Nguyen-code/TVCRocket/Software/Reference/aeroForcesCalc1.jpg

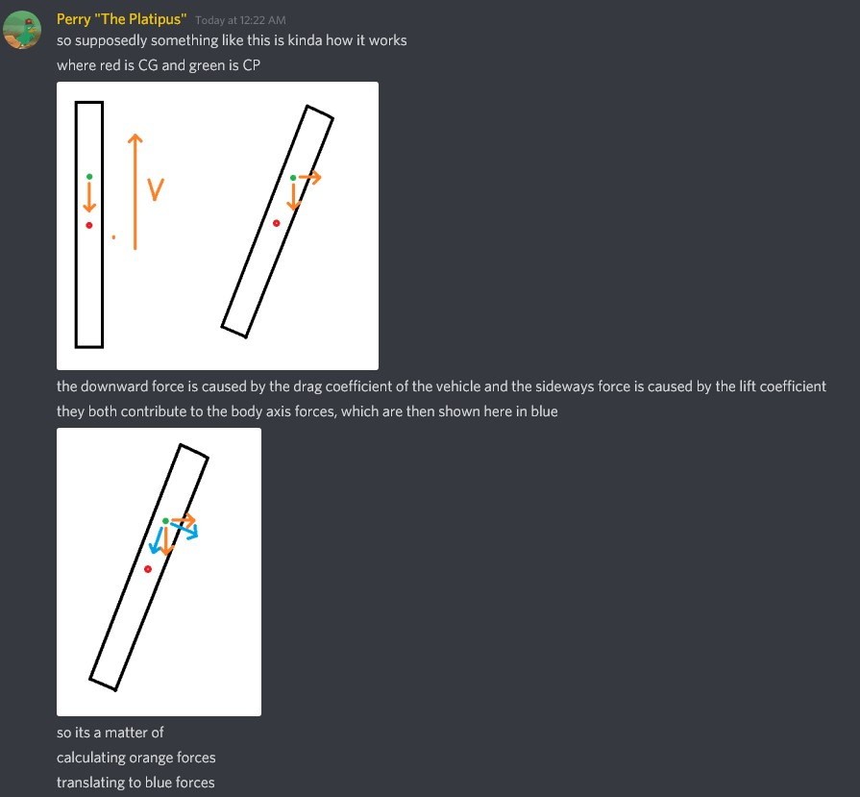
Software/Reference/aeroForcesCalc1.jpg
