Nguyen-code/TVCRocket/Software/Reference/aeroForcesCalc2.jpg

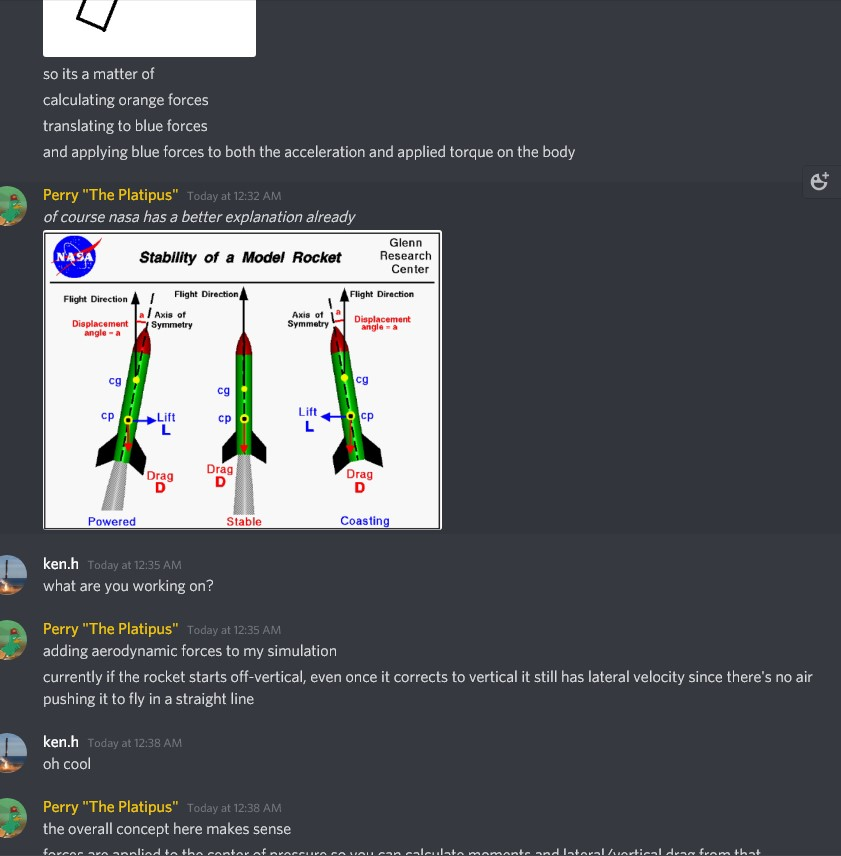
Software/Reference/aeroForcesCalc2.jpg
