Nguyen-code/TVCRocket/Software/Reference/aeroForcesCalc3.jpg

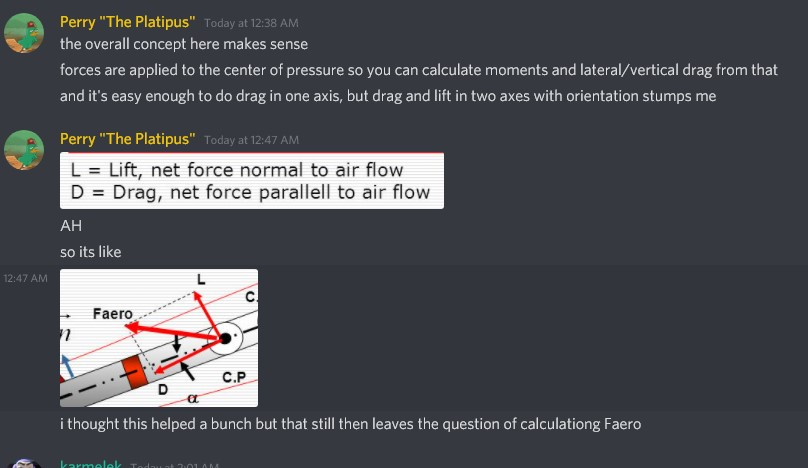
Software/Reference/aeroForcesCalc3.jpg
