Nguyen-code/TVCRocket/Software/Reference/axesCheck.jpg

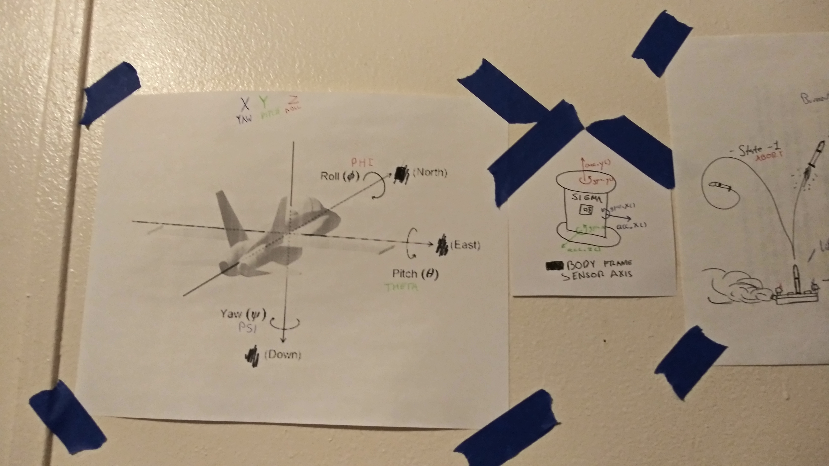
Software/Reference/axesCheck.jpg
