Nguyen-code/TVCRocket/Software/Reference/BEST PROPER USB DIAGRAM.jpg

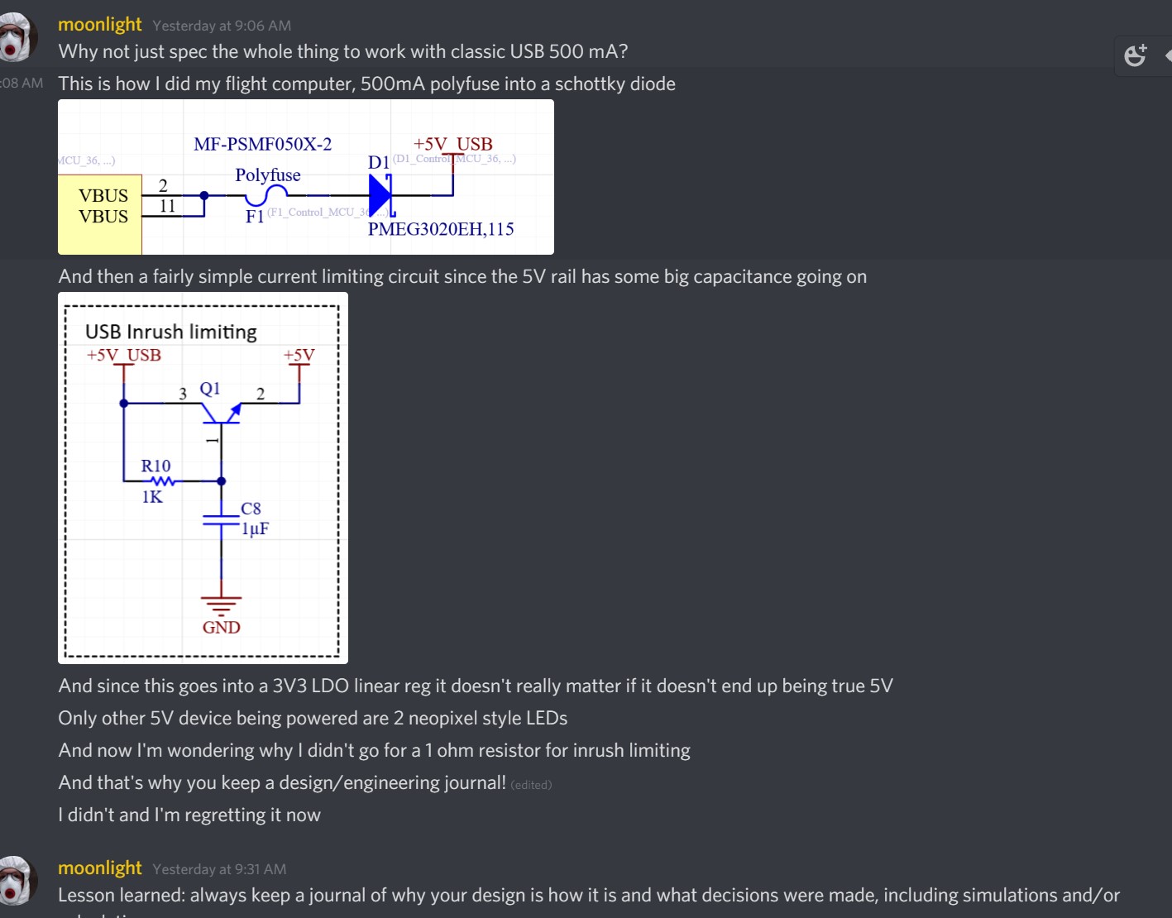
Software/Reference/BEST PROPER USB DIAGRAM.jpg
