Nguyen-code/TVCRocket/Software/Reference/bitfields.jpg

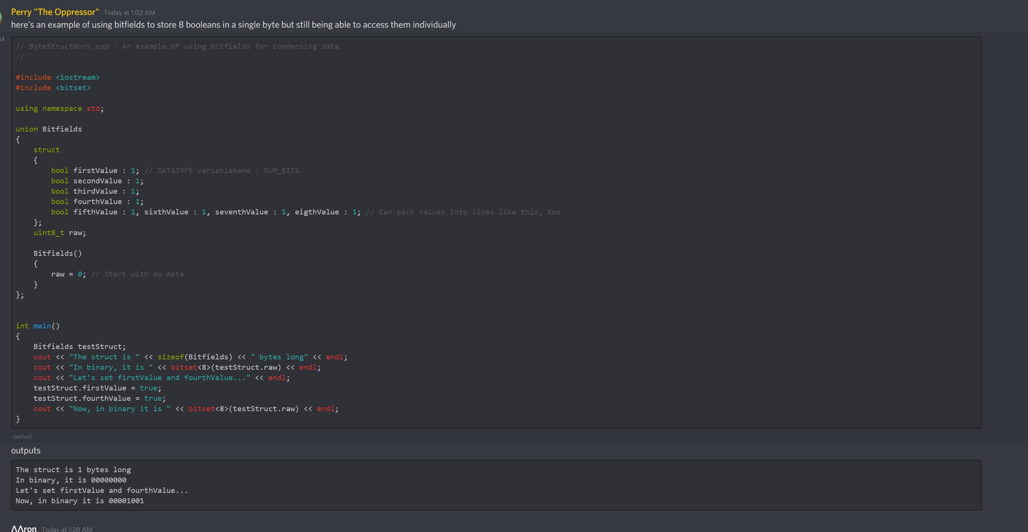
Software/Reference/bitfields.jpg
