Nguyen-code/TVCRocket/Software/Reference/dma spi.jpg

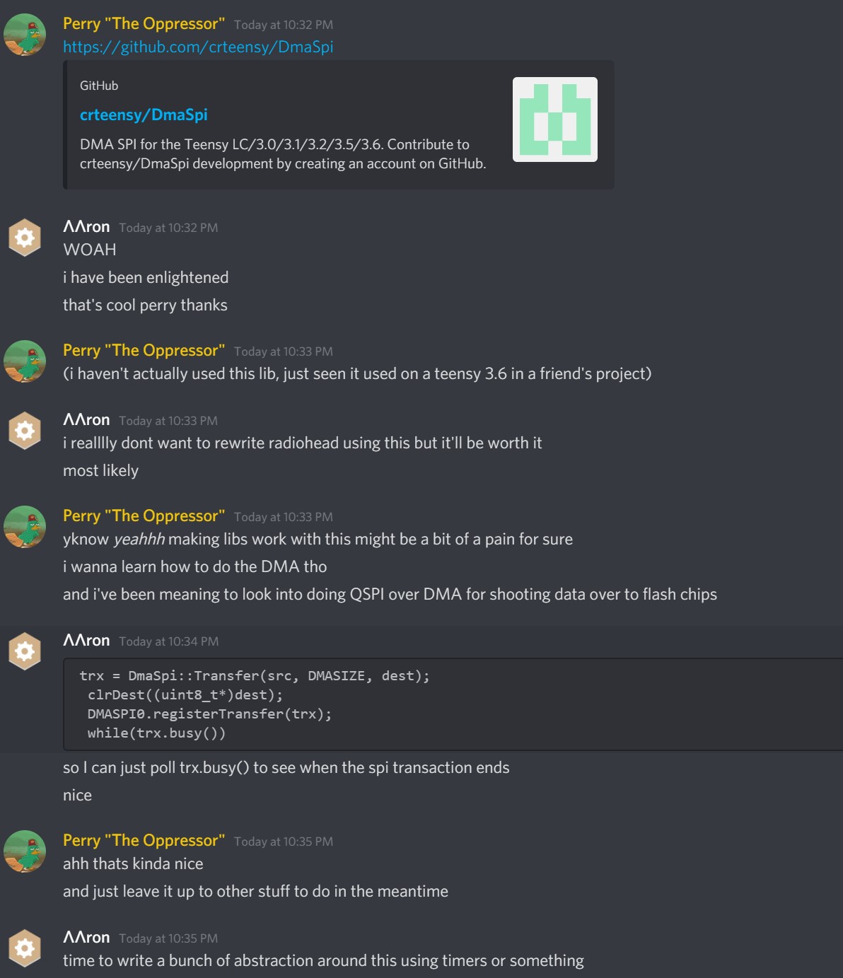
Software/Reference/dma spi.jpg
