Nguyen-code/TVCRocket/Software/Reference/drag and tvc.jpg

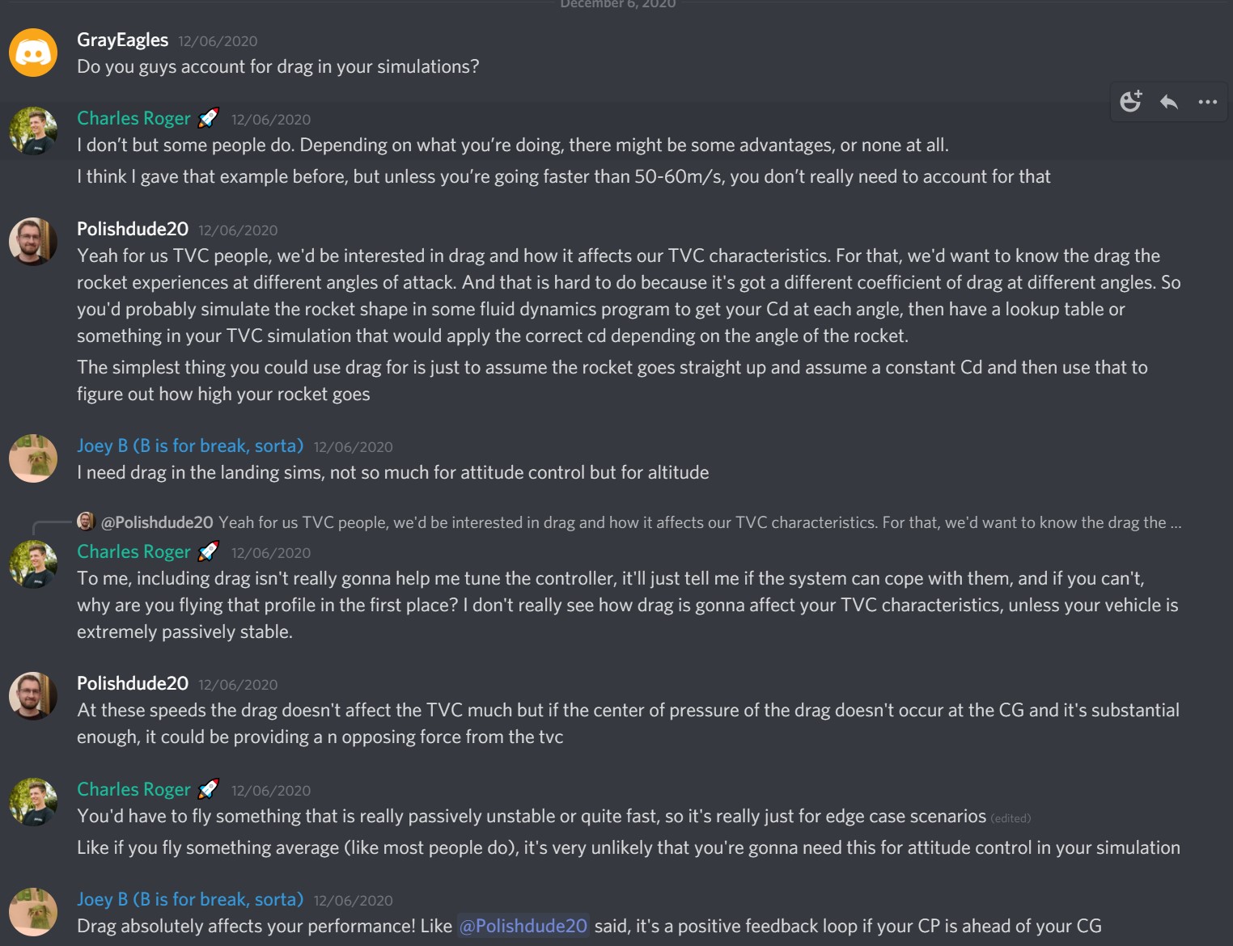
Software/Reference/drag and tvc.jpg
