Nguyen-code/TVCRocket/Software/Reference/ground software idea.jpg

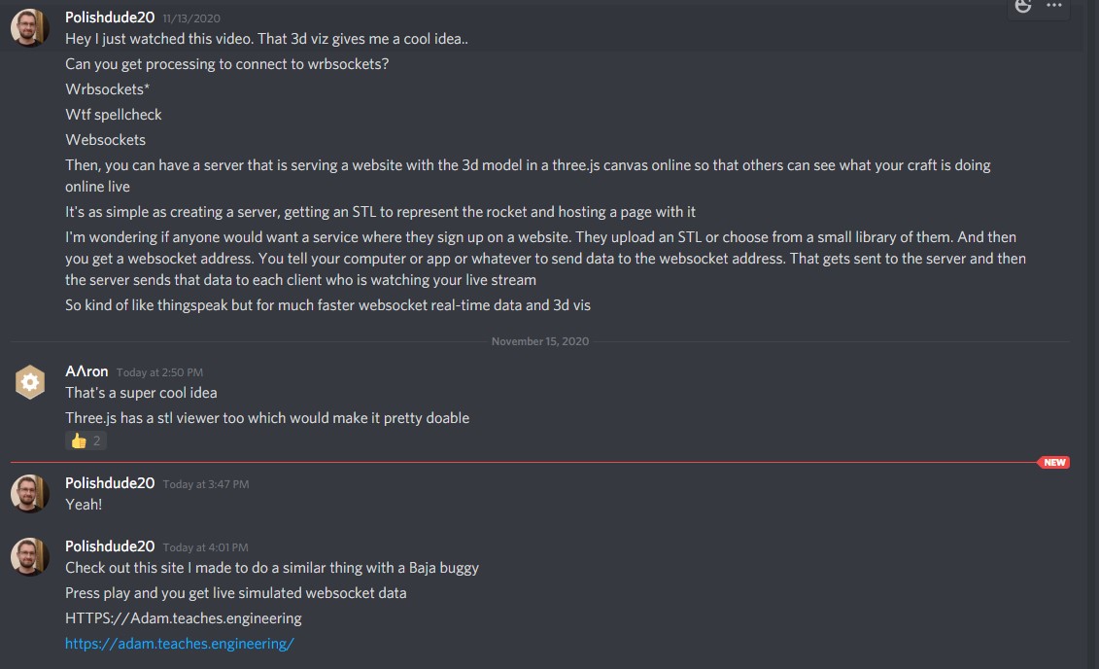
Software/Reference/ground software idea.jpg
