Nguyen-code/TVCRocket/Software/Reference/Holddown_base_v1.png

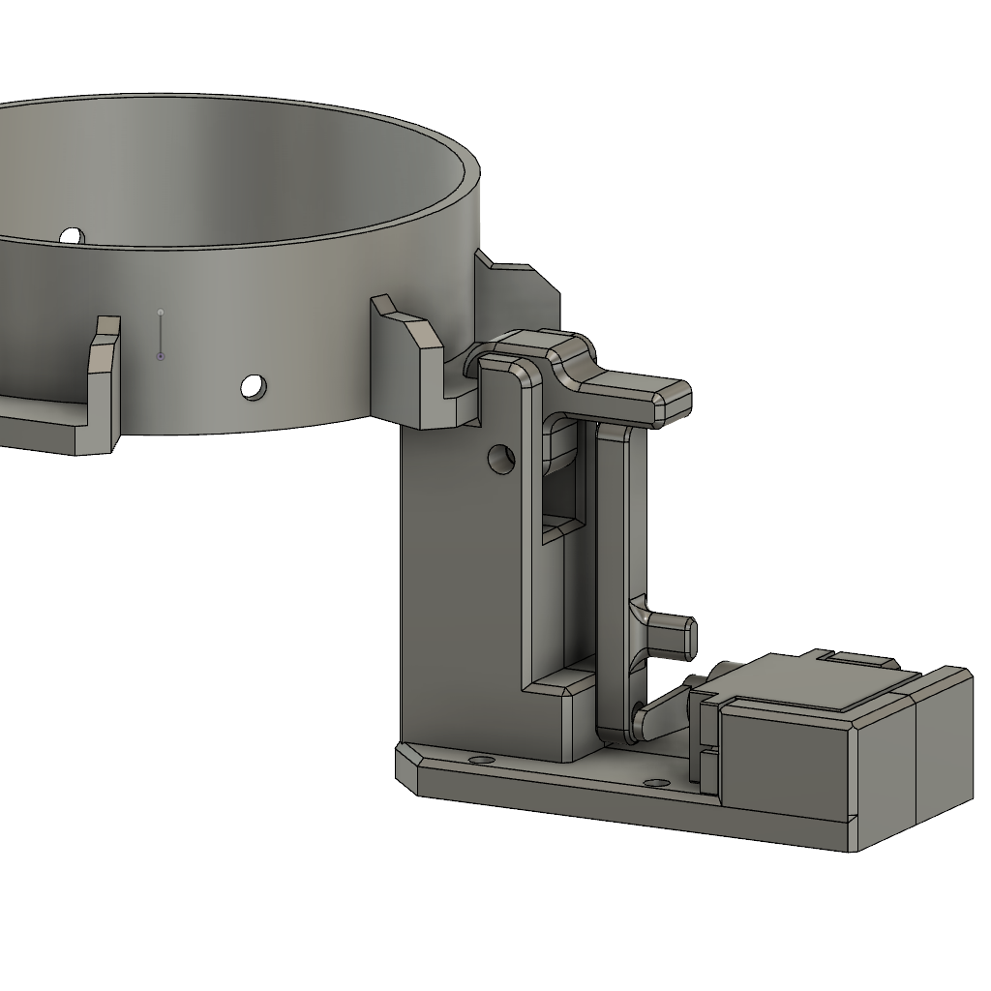
Software/Reference/Holddown_base_v1.png
