Nguyen-code/TVCRocket/Software/Reference/liftoff ori.jpg

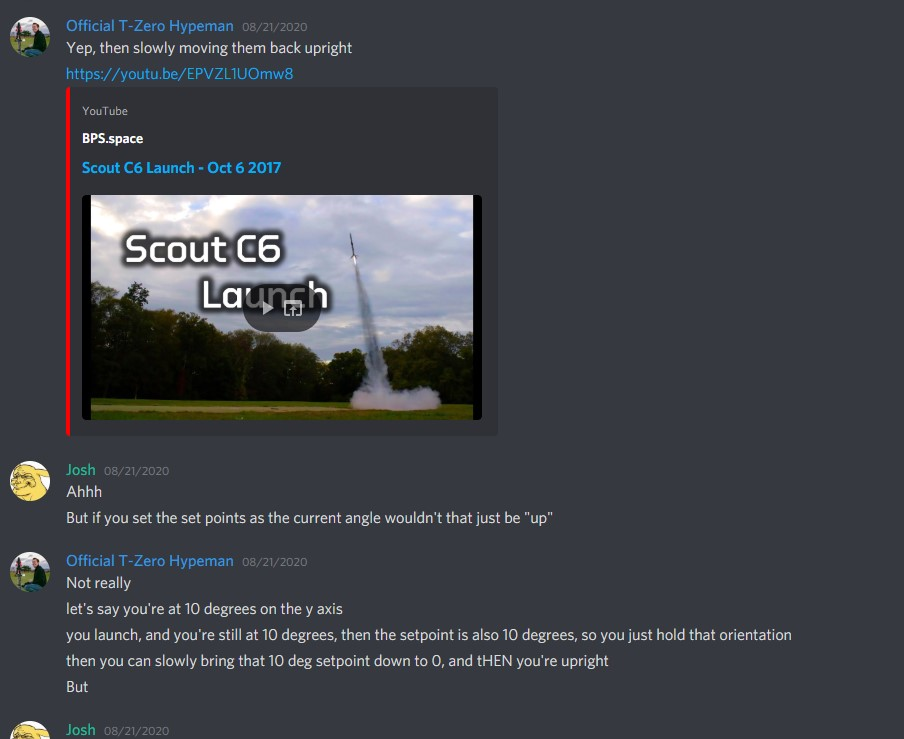
Software/Reference/liftoff ori.jpg
