Nguyen-code/TVCRocket/Software/Reference/local-global quat.jpg

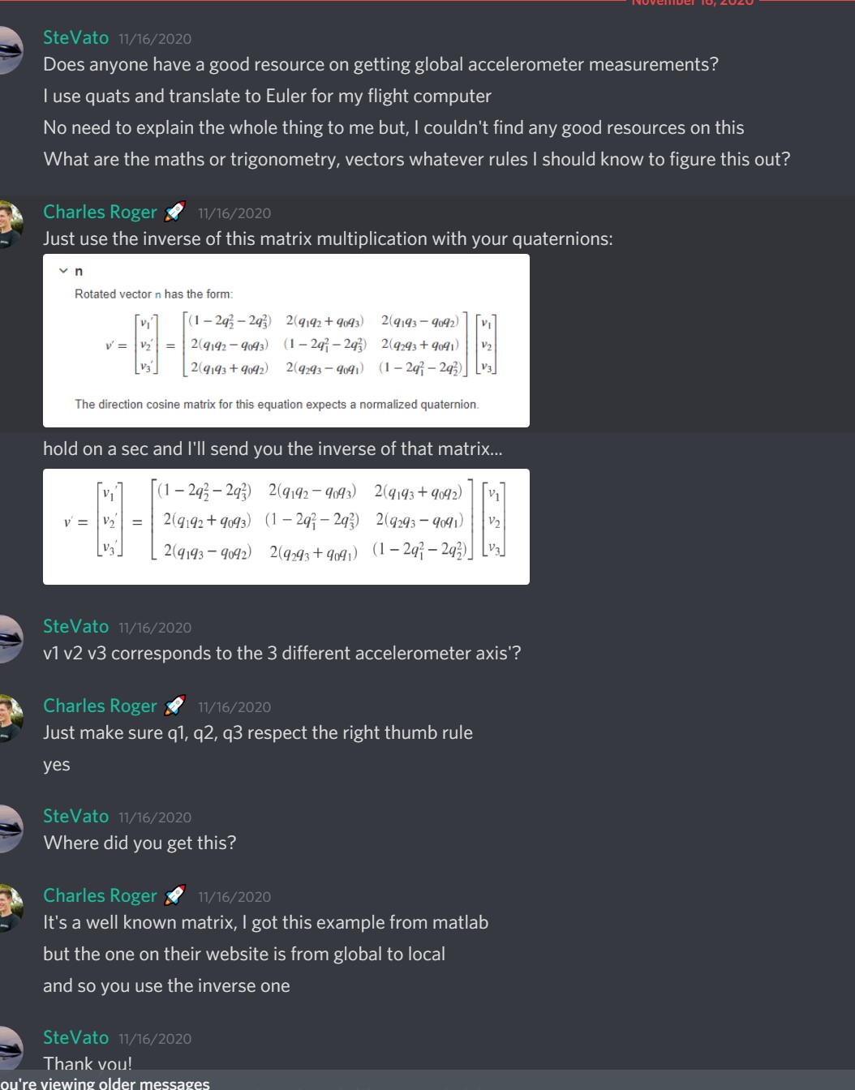
Software/Reference/local-global quat.jpg
