Nguyen-code/TVCRocket/Software/Reference/mag complementary filter.jpg

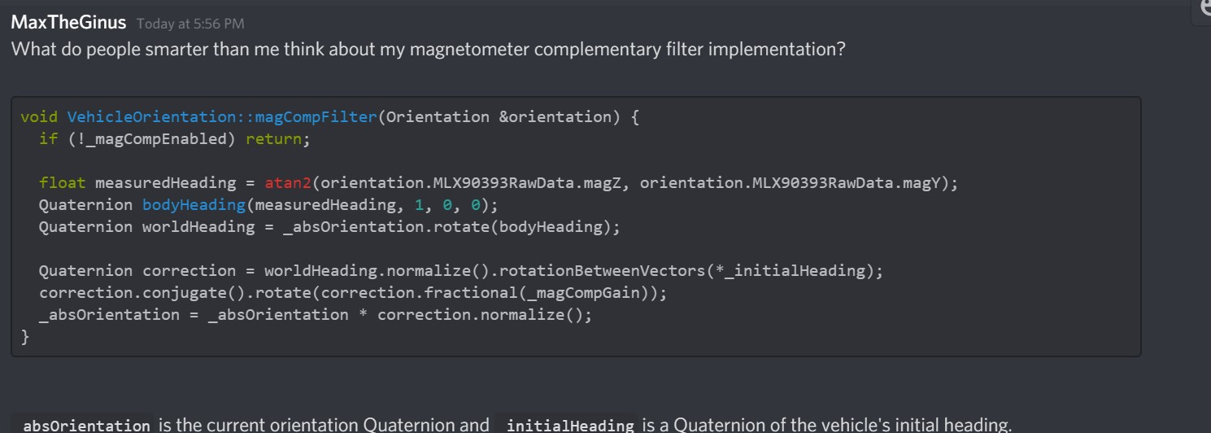
Software/Reference/mag complementary filter.jpg
