Nguyen-code/TVCRocket/Software/Reference/memz.png

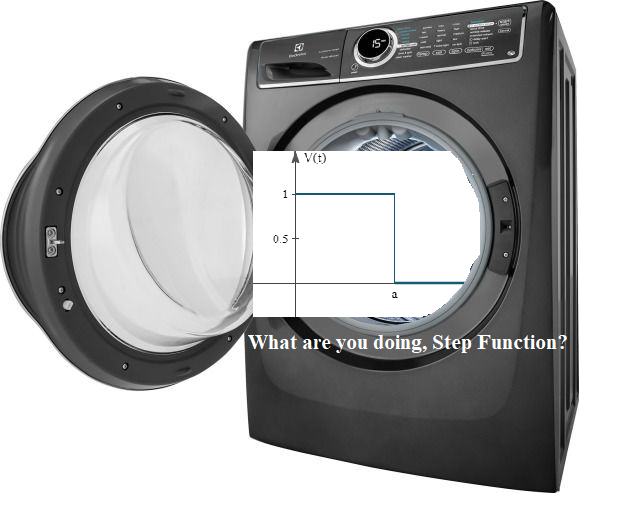
Software/Reference/memz.png
