Nguyen-code/TVCRocket/Software/Reference/mmoi eqn.jpg

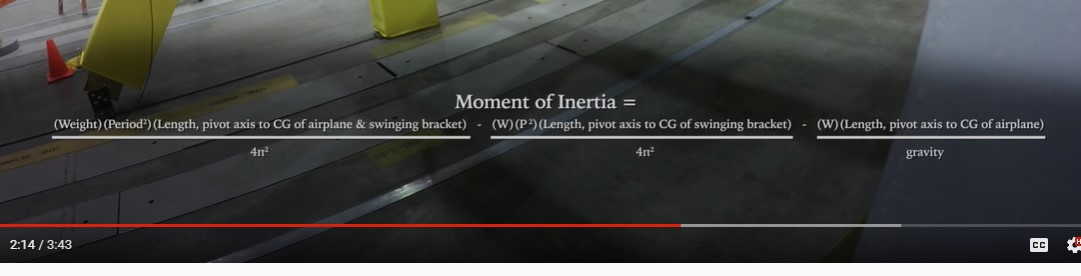
Software/Reference/mmoi eqn.jpg
