Nguyen-code/TVCRocket/Software/Reference/more tvc diode usb stuff.jpg

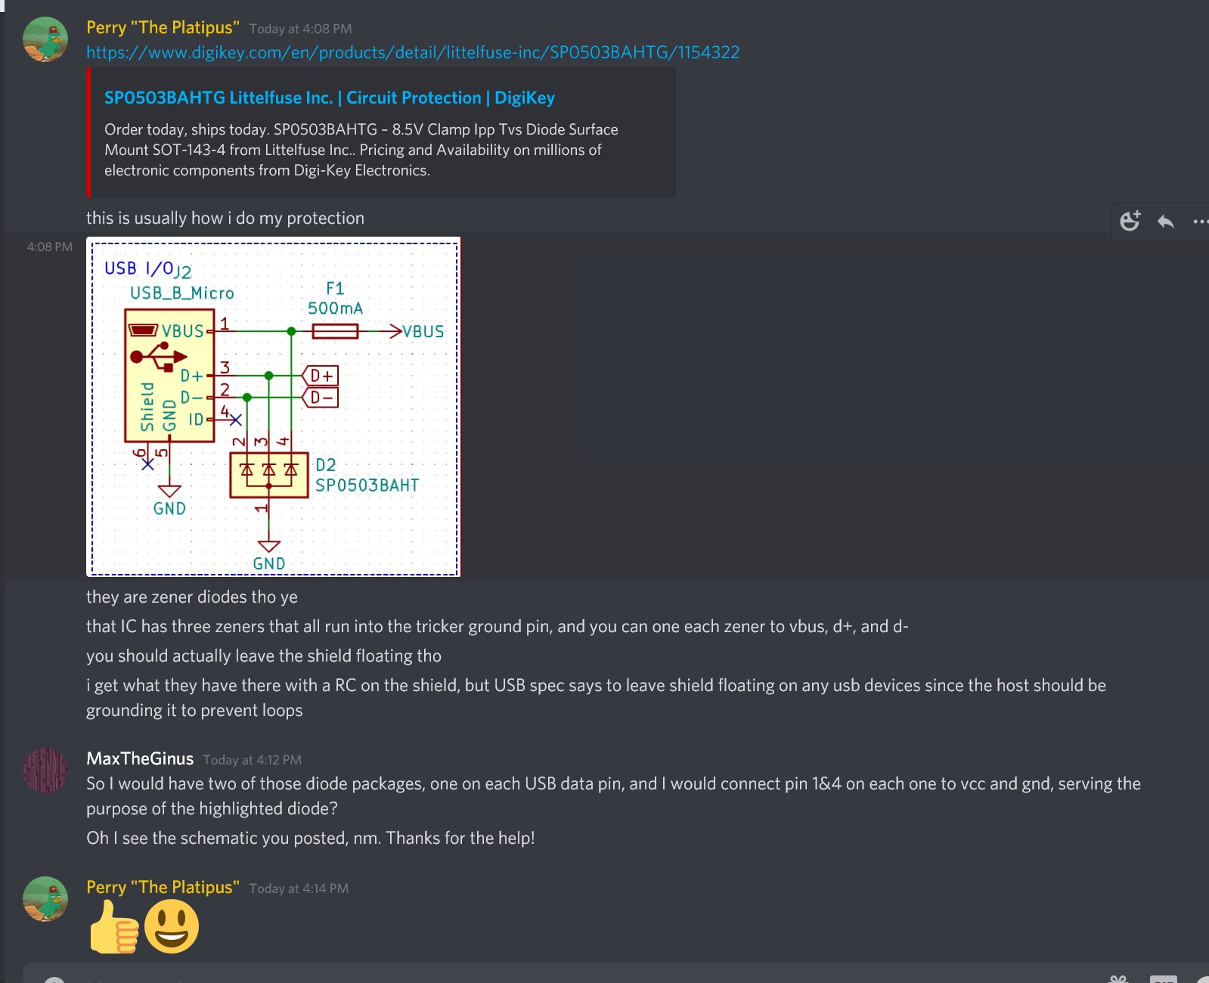
Software/Reference/more tvc diode usb stuff.jpg
