Nguyen-code/TVCRocket/Software/Reference/moreRollWheelControl.jpg

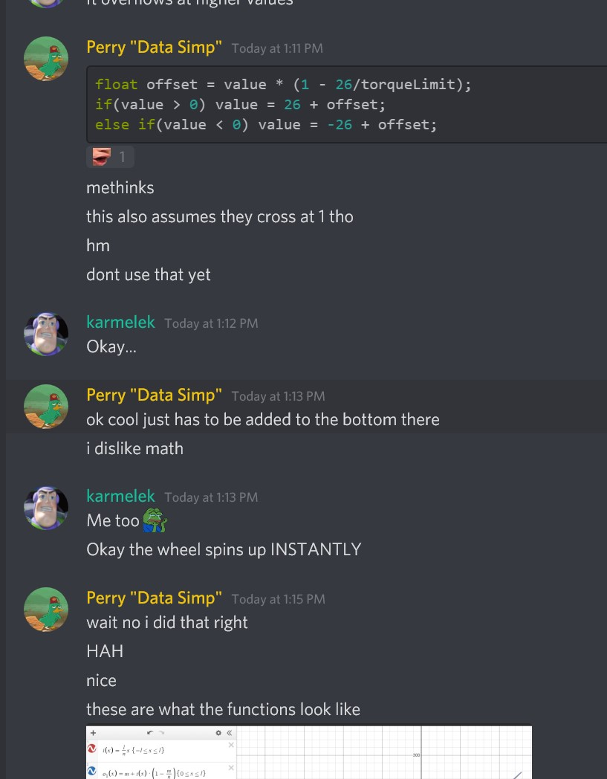
Software/Reference/moreRollWheelControl.jpg
