Nguyen-code/TVCRocket/Software/Reference/morezeroorderhold.png

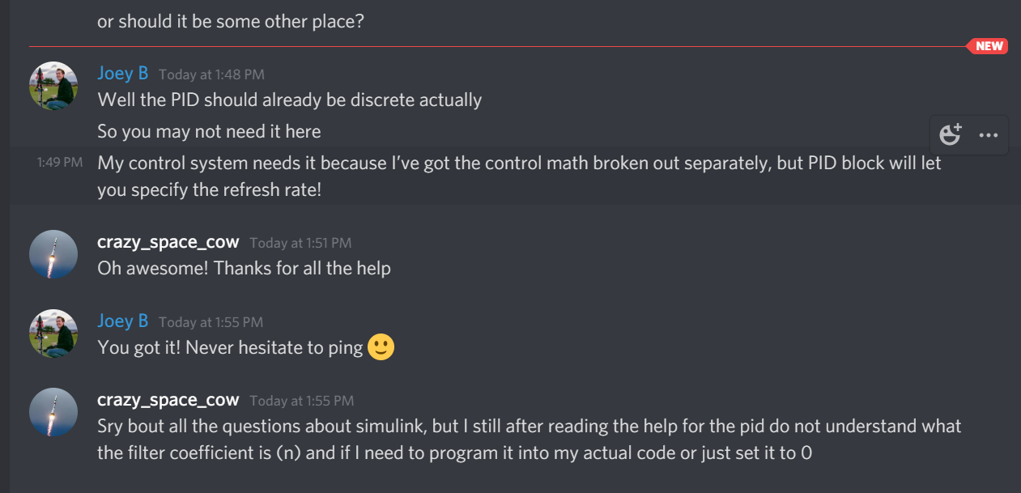
Software/Reference/morezeroorderhold.png
