Nguyen-code/TVCRocket/Software/Reference/nonblocking - use return type of a nonblocking float w status boolean and data.jpg

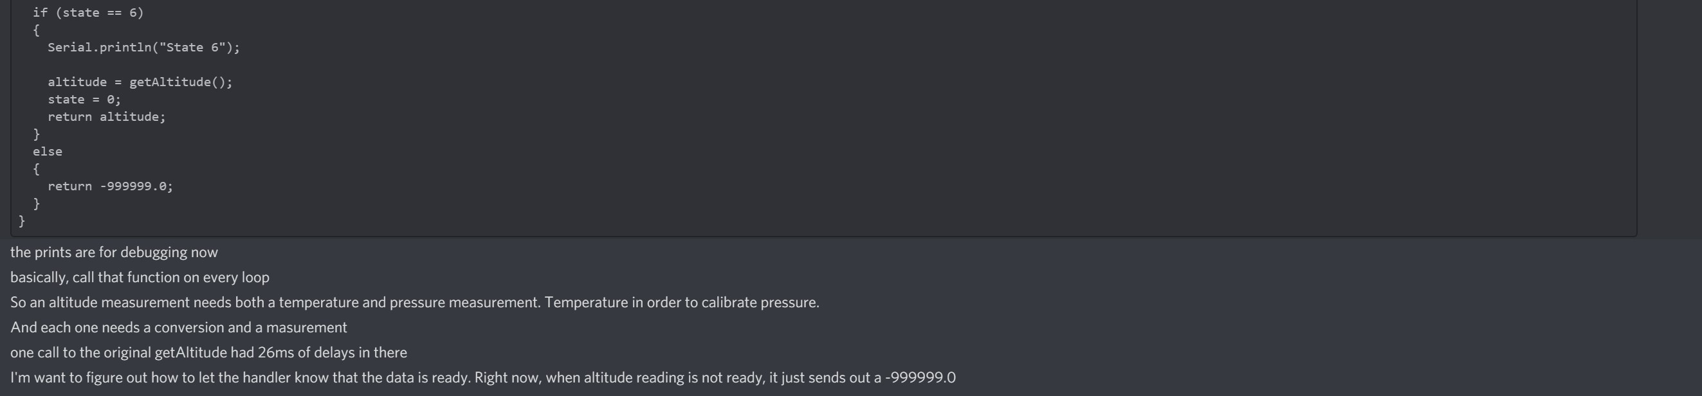
Software/Reference/nonblocking - use return type of a nonblocking float w status boolean and data.jpg
