Nguyen-code/TVCRocket/Software/Reference/pitchManuever.PNG

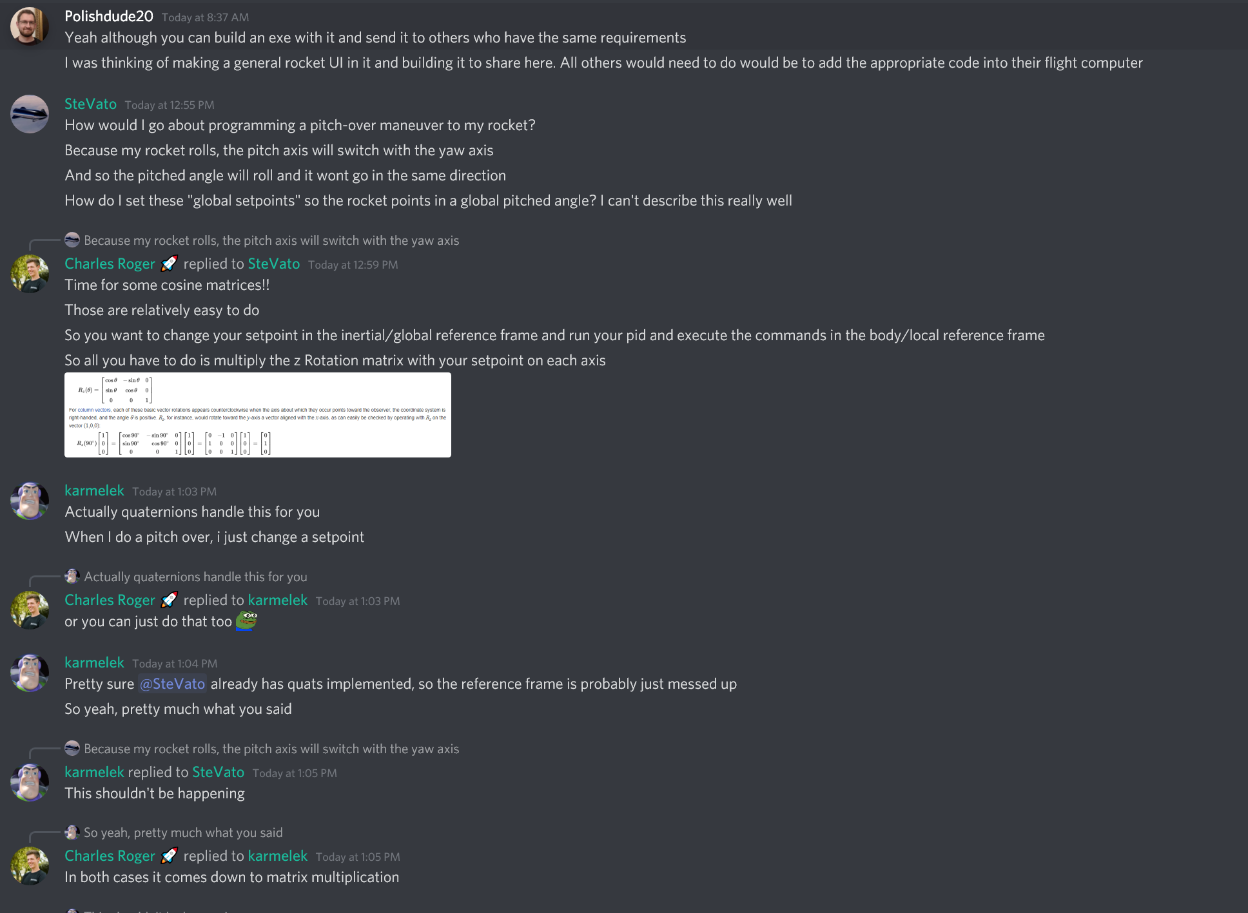
Software/Reference/pitchManuever.PNG
