Nguyen-code/TVCRocket/Software/Reference/quat to ang.jpg

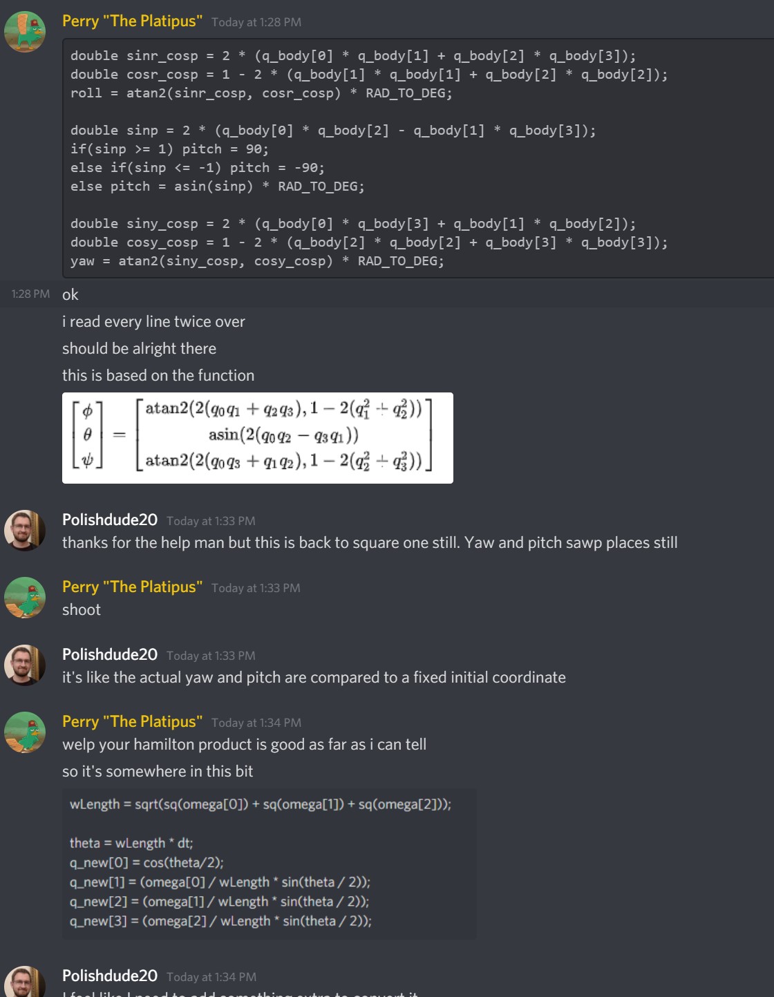
Software/Reference/quat to ang.jpg
