Nguyen-code/TVCRocket/Software/Reference/ref quat ori.png

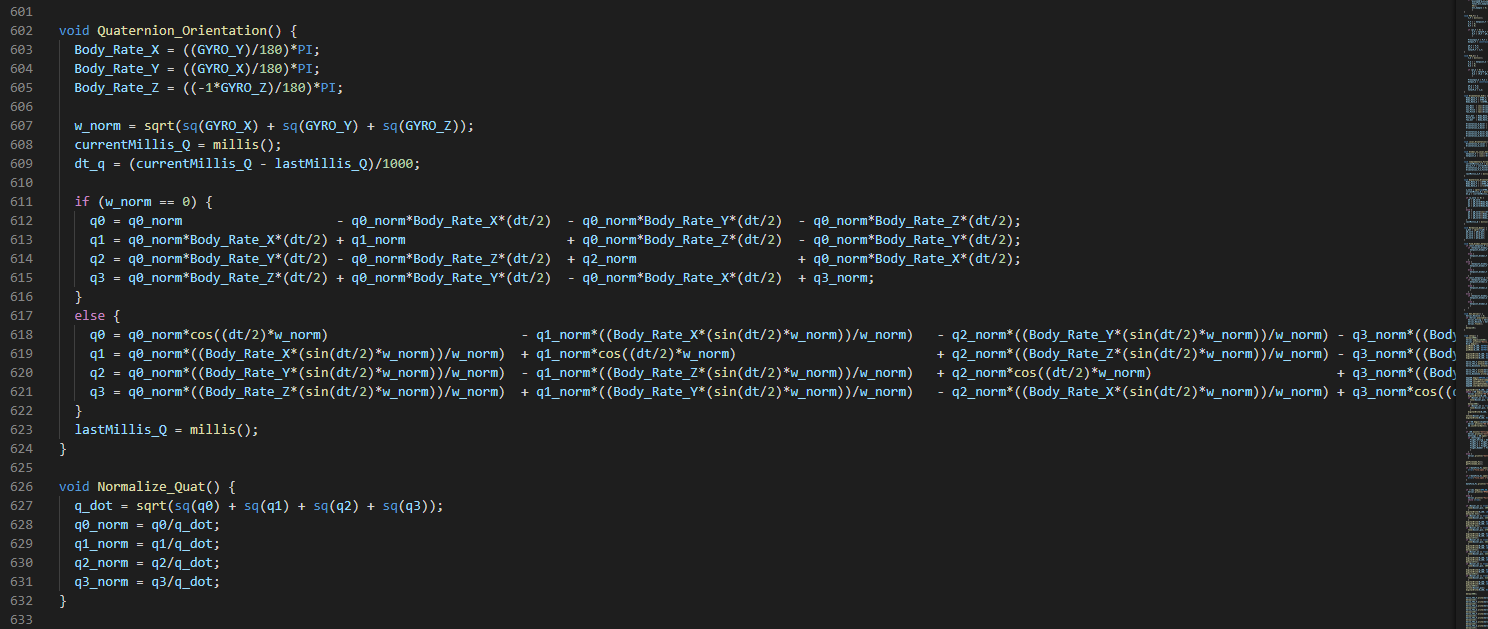
Software/Reference/ref quat ori.png
