Nguyen-code/TVCRocket/Software/Reference/rh v lh coordinate inertial to body.PNG

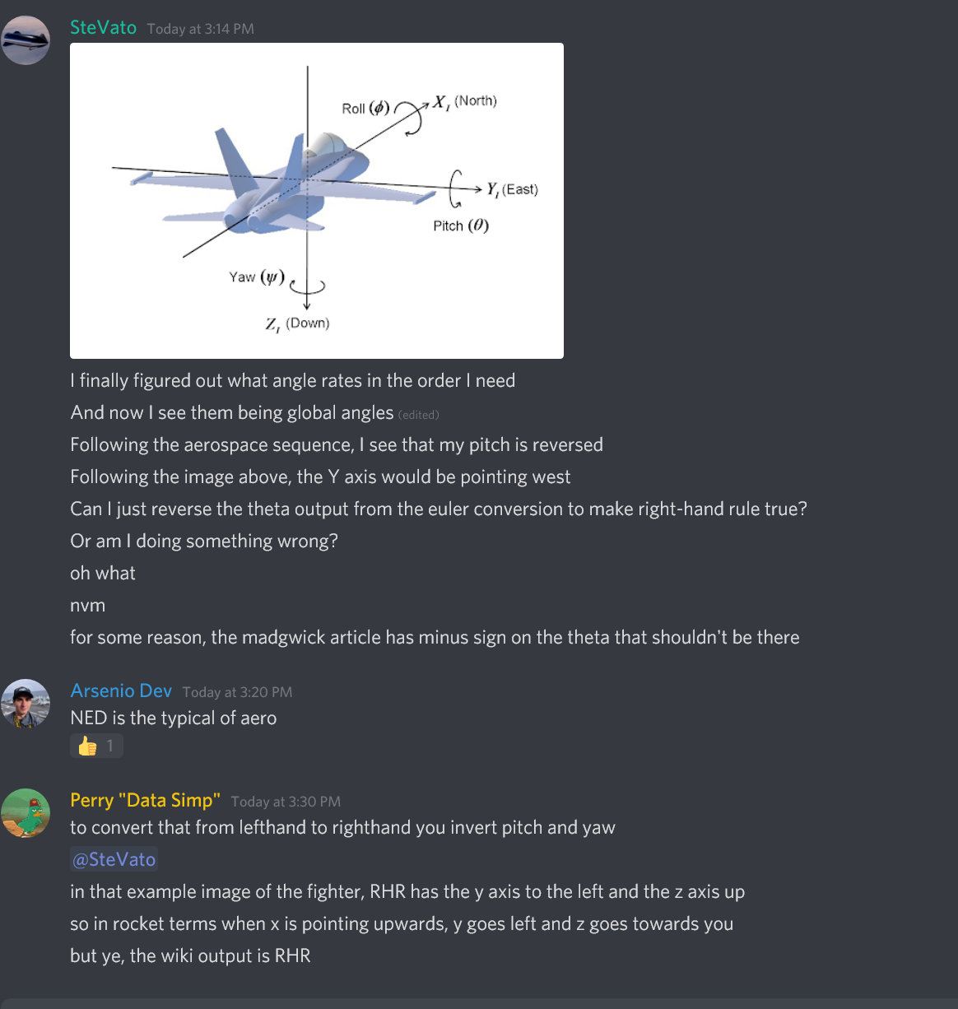
Software/Reference/rh v lh coordinate inertial to body.PNG
