Nguyen-code/TVCRocket/Software/Reference/rollControlcodes.jpg

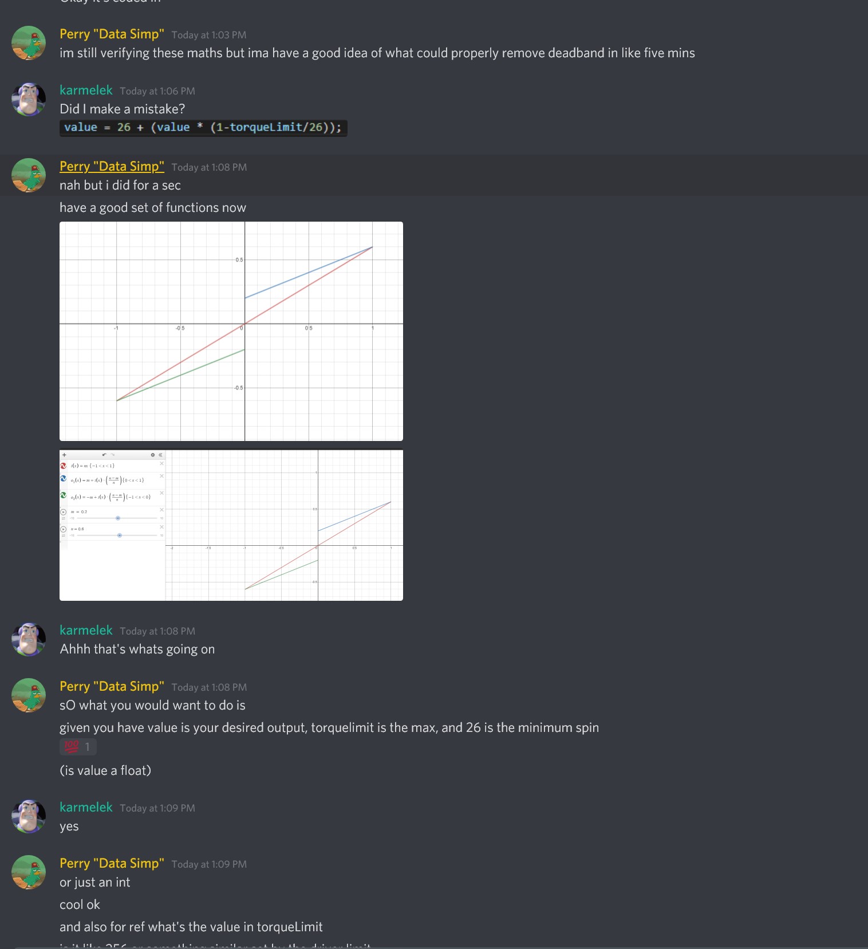
Software/Reference/rollControlcodes.jpg
