Nguyen-code/TVCRocket/Software/Reference/Screenshot 2020-10-27 151349.png

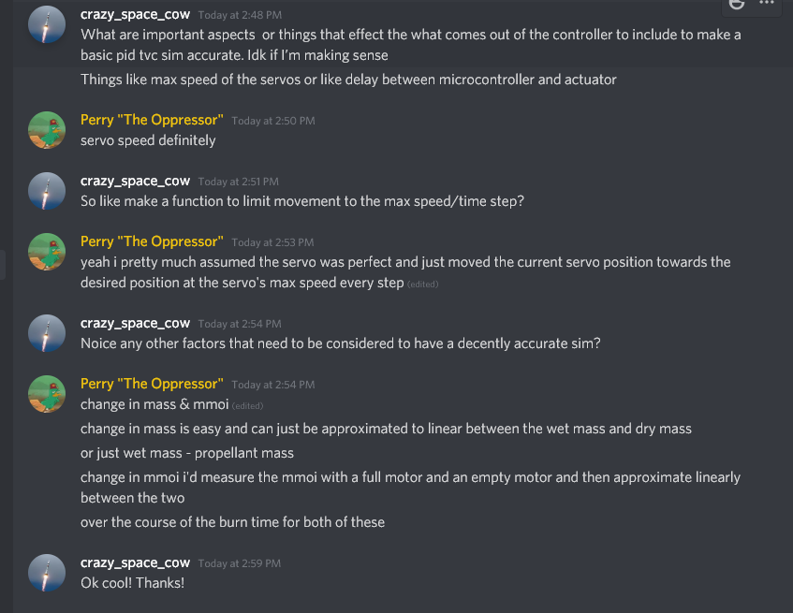
Software/Reference/Screenshot 2020-10-27 151349.png
