Nguyen-code/TVCRocket/Software/Reference/simulink2.png

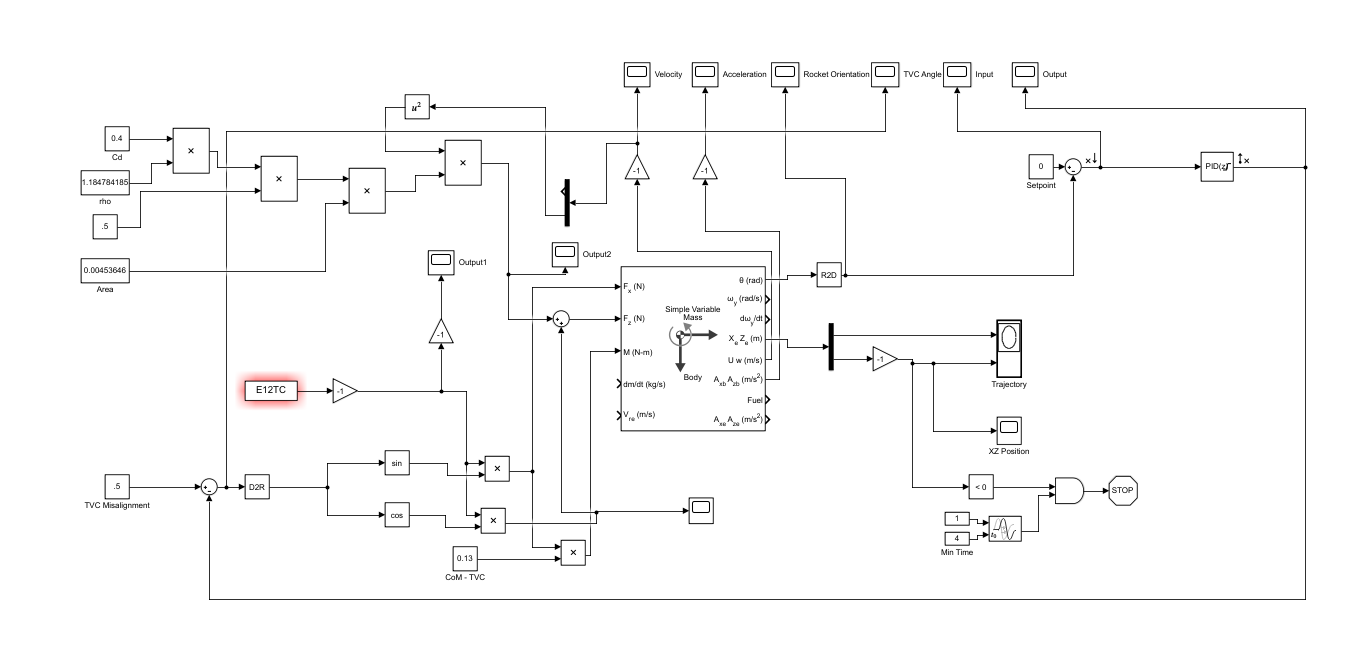
Software/Reference/simulink2.png
