Nguyen-code/TVCRocket/Software/Reference/take into account pdop and gnss undertainty in kalman.jpg

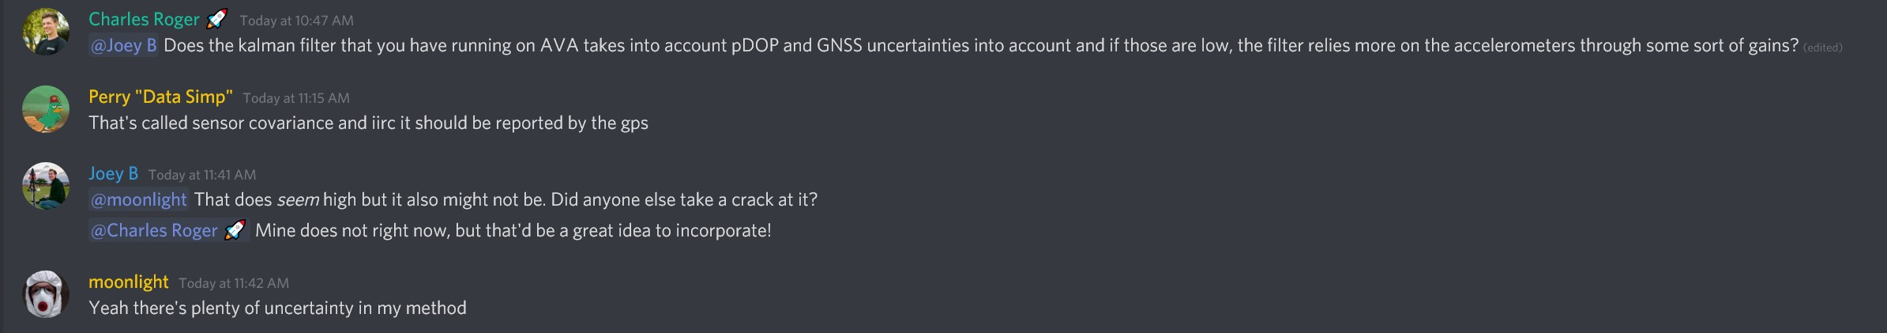
Software/Reference/take into account pdop and gnss undertainty in kalman.jpg
