Nguyen-code/TVCRocket/Software/Reference/unionreminder.jpg

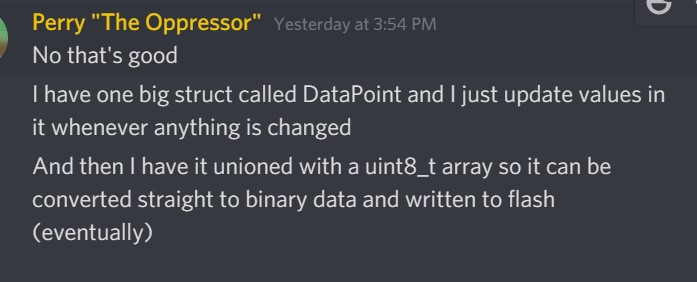
Software/Reference/unionreminder.jpg
