Nguyen-code/TVCRocket/Software/Reference/way to find COM.jpg

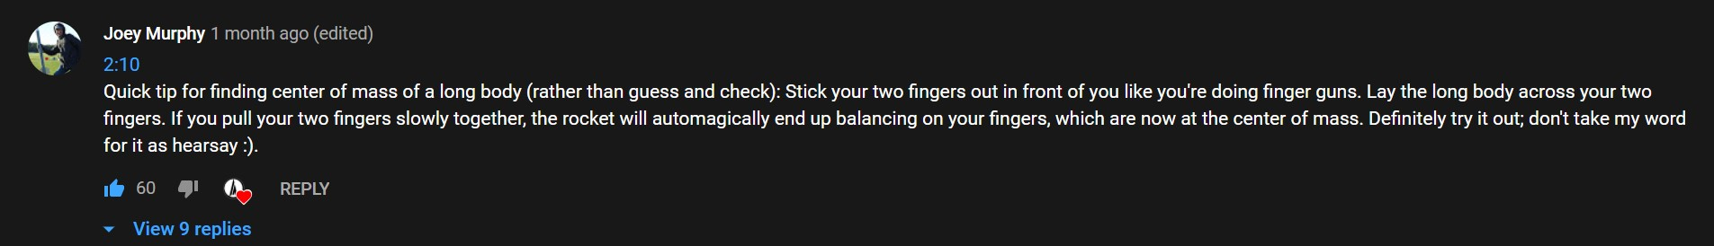
Software/Reference/way to find COM.jpg
