Nguyen-code/TVCRocket/Software/Reference/zerorderHoldSimulink.png

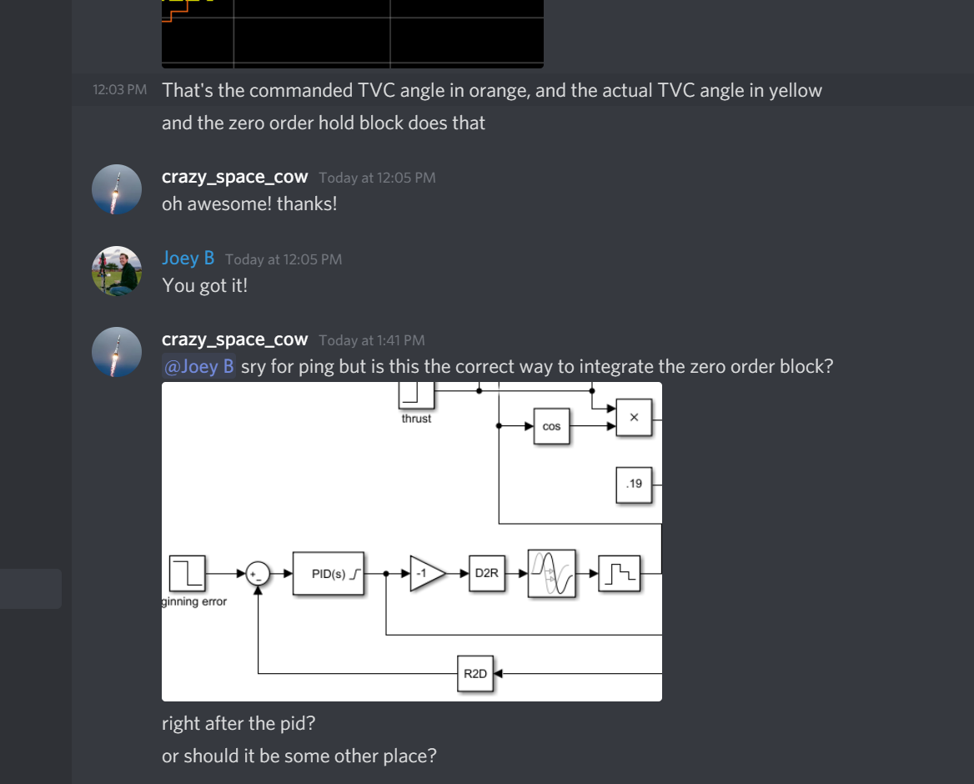
Software/Reference/zerorderHoldSimulink.png
