Nguyen-code/TVCRocket/Mechanical Design/manf/topMountP1v2.sldprt

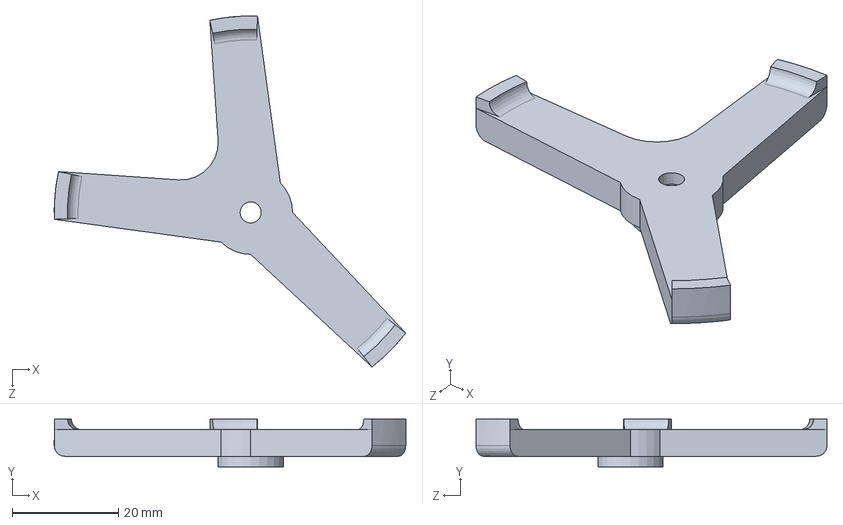
[picture p59: CAD file, 2020-10-10]
Mechanical Design/manf/topMountP1v2.sldprt
66.2 x 9.00 x 66.1 mm
