Nguyen-code/TVCRocket/Mechanical Design/manf/topMountP1v3.sldprt

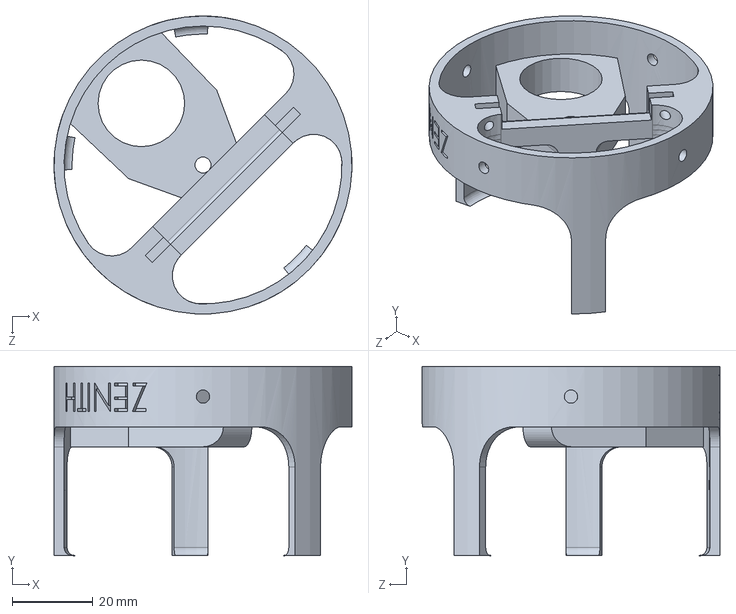
[picture p60: CAD file, 2020-10-10]
Mechanical Design/manf/topMountP1v3.sldprt
74.0 x 47.0 x 74.0 mm
