Nguyen-code/TVCRocket/Mechanical Design/guidanceComputerMount/guidance mount bottom.SLDPRT

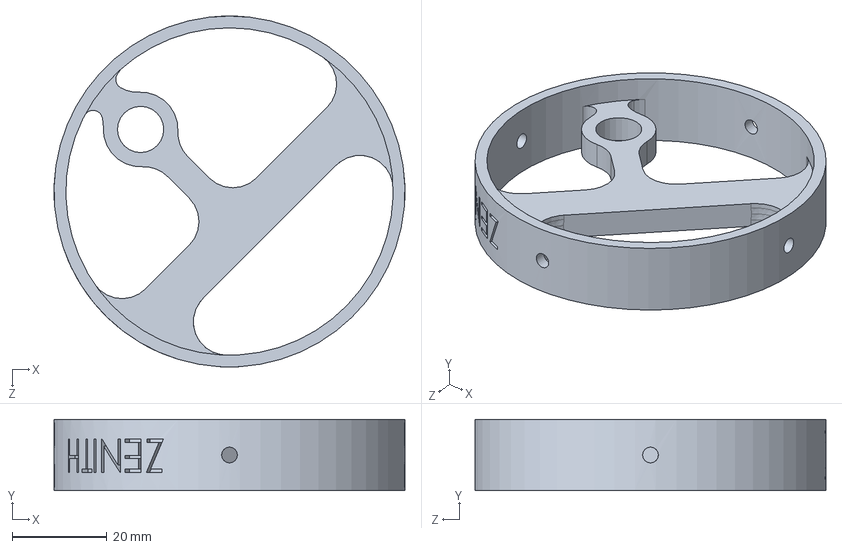
[picture p61: CAD file, 2020-10-10]
Mechanical Design/guidanceComputerMount/guidance mount bottom.SLDPRT
74.0 x 15.0 x 74.0 mm
