Nguyen-code/TVCRocket/Mechanical Design/manf/clampingSpacer.STL

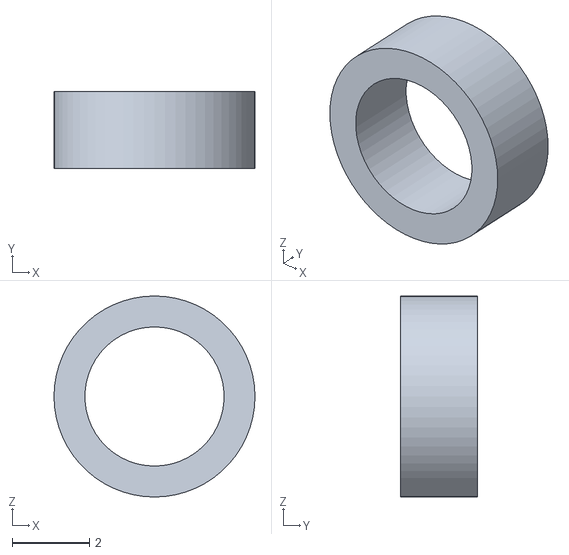
[picture p62: CAD file, 2020-10-10]
Mechanical Design/manf/clampingSpacer.STL
5.20 x 2.00 x 5.20
