Nguyen-code/TVCRocket/Mechanical Design/testMount.SLDPRT

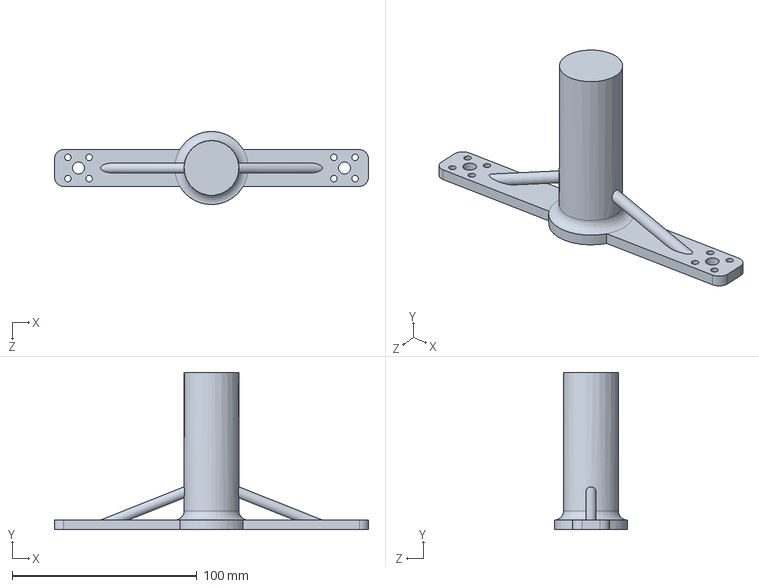
[picture p63: CAD file, 2020-10-10]
Mechanical Design/testMount.SLDPRT
170.0 x 85.2 x 39.6 mm
