Nguyen-code/TVCRocket/Mechanical Design/gimbalOuter.SLDPRT

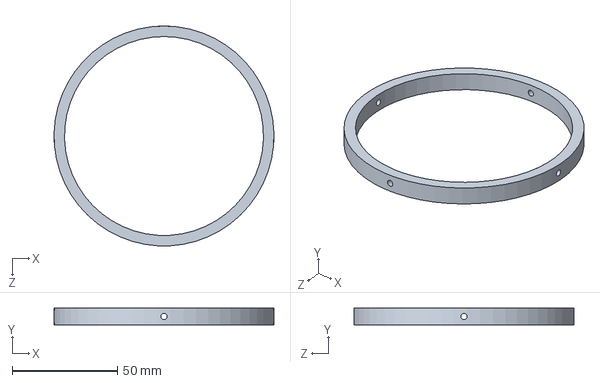
[picture p64: CAD file, 2020-10-10]
Mechanical Design/gimbalOuter.SLDPRT
104.5 x 8.00 x 104.5 mm
