Nguyen-code/TVCRocket/Mechanical Design/manf/topMountP2v3.sldprt

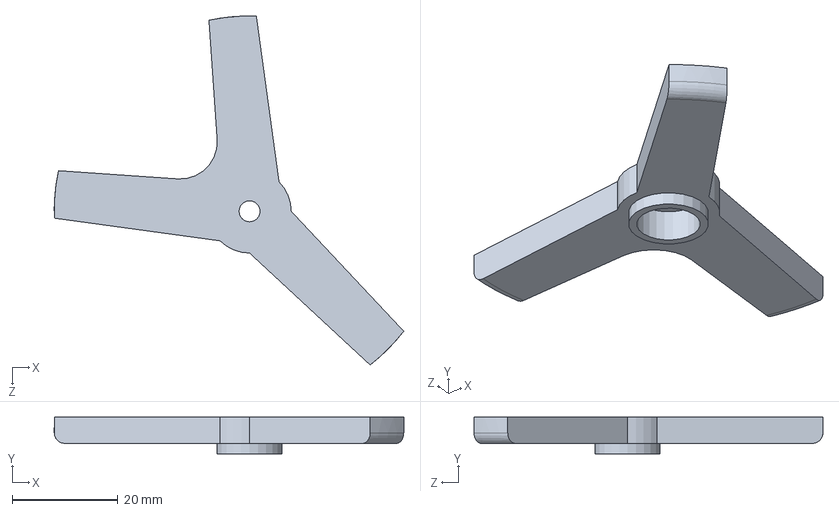
[picture p65: CAD file, 2020-10-10]
Mechanical Design/manf/topMountP2v3.sldprt
66.2 x 7.00 x 66.1 mm
