Nguyen-code/TVCRocket/Mechanical Design/gimbalOutside.SLDPRT

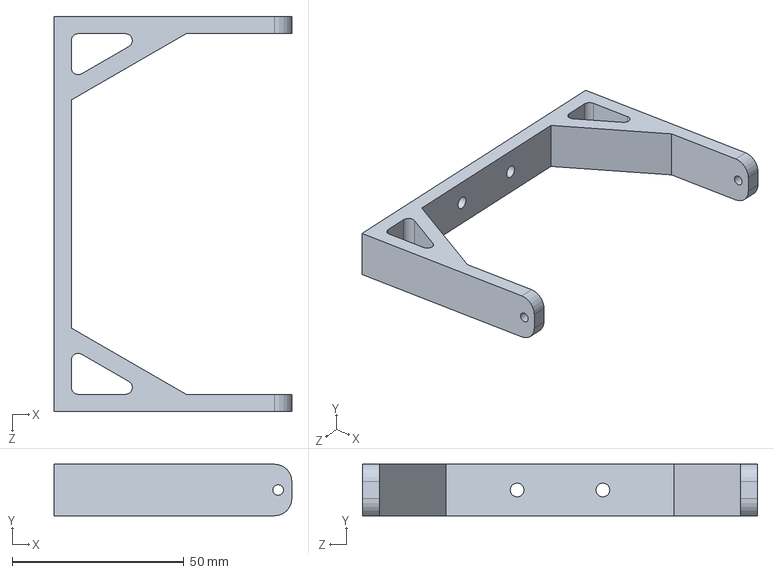
[picture p66: CAD file, 2020-10-10]
Mechanical Design/gimbalOutside.SLDPRT
69.2 x 15.0 x 115.0 mm
