Nguyen-code/TVCRocket/Mechanical Design/manf/gimbalInner.STL

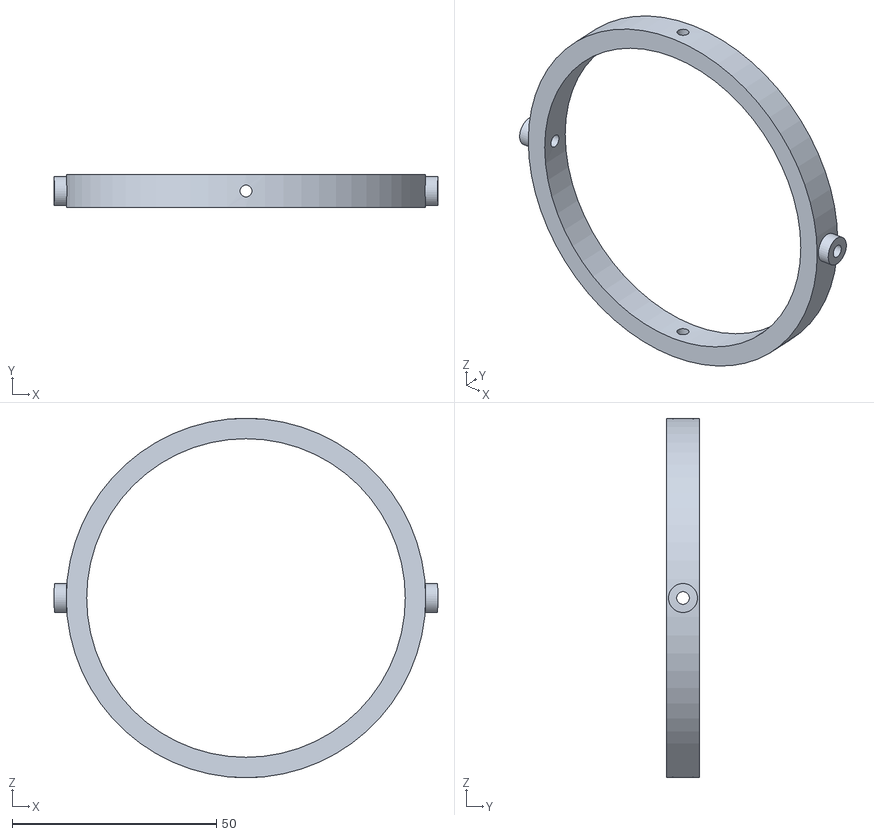
[picture p67: CAD file, 2020-10-10]
Mechanical Design/manf/gimbalInner.STL
94.0 x 8.00 x 88.0
