Nguyen-code/TVCRocket/Mechanical Design/guidanceComputerMount/guidance mount top.SLDPRT

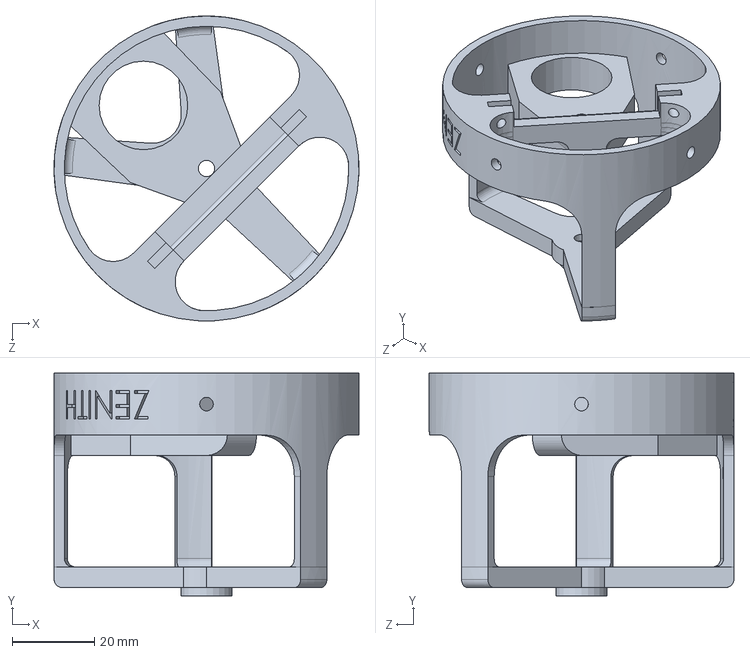
[picture p68: CAD file, 2020-10-10]
Mechanical Design/guidanceComputerMount/guidance mount top.SLDPRT
74.0 x 54.0 x 74.0 mm
