Nguyen-code/TVCRocket/Mechanical Design/body tube top.SLDPRT

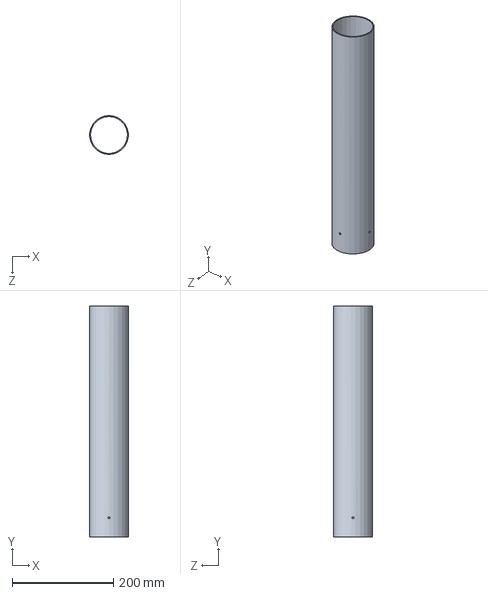
[picture p69: CAD file, 2020-10-02]
Mechanical Design/body tube top.SLDPRT
77.0 x 457.2 x 77.0 mm
