Nguyen-code/TVCRocket/Mechanical Design/guidanceComputerMount/antenna.SLDPRT

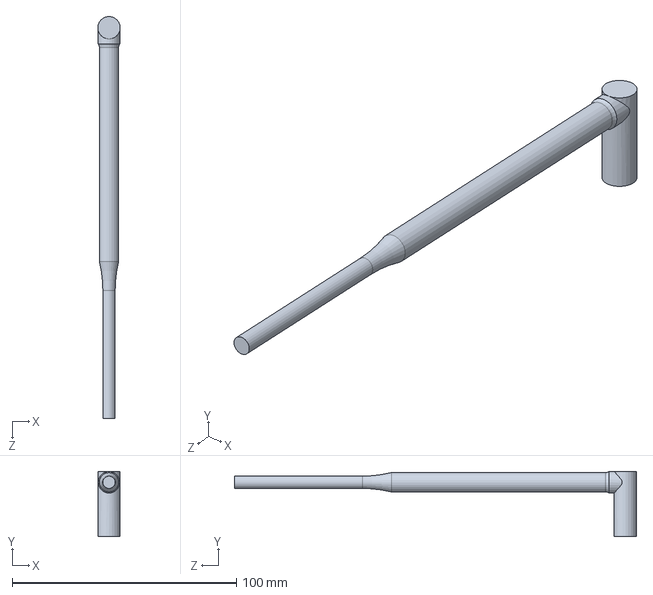
[picture p70: CAD file, 2020-10-02]
Mechanical Design/guidanceComputerMount/antenna.SLDPRT
10.0 x 29.0 x 179.3 mm
