Nguyen-code/TVCRocket/Mechanical Design/manf/all gimbal stuff.3mf

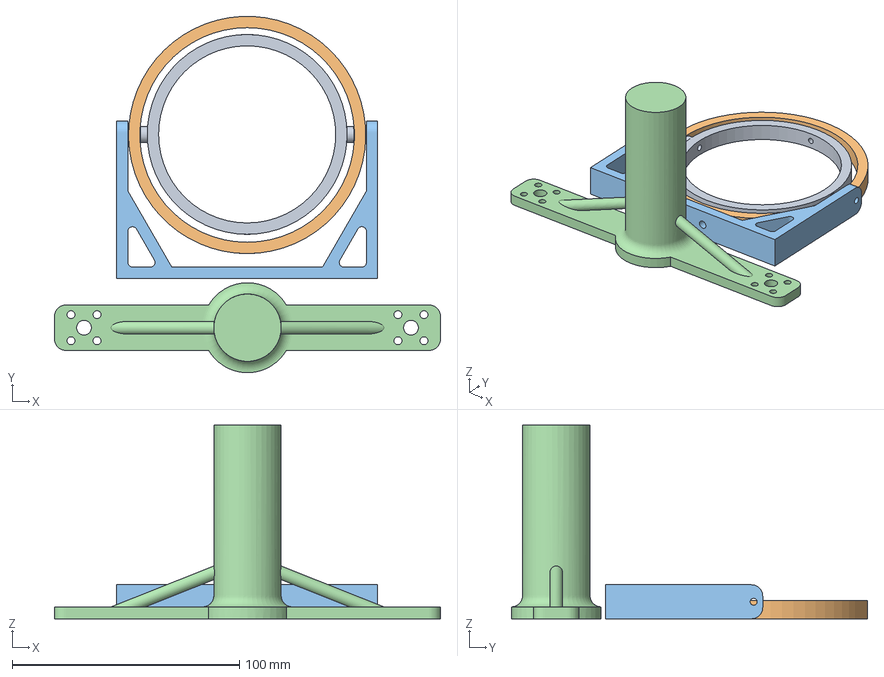
[picture p71: CAD file, 2020-10-10]
Mechanical Design/manf/all gimbal stuff.3mf
170.0 x 156.9 x 85.3 mm
gimbalInner.STL
gimbalOuter.STL
gimbalOutside.STL
testMount.STL
