Nguyen-code/TVCRocket/Mechanical Design/guidanceComputerMount/rollmotor.SLDPRT

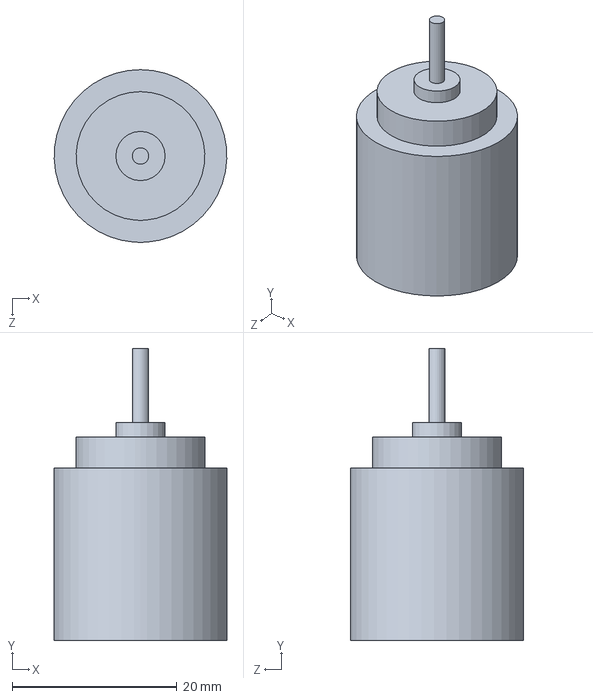
[picture p72: CAD file, 2020-10-02]
Mechanical Design/guidanceComputerMount/rollmotor.SLDPRT
21.0 x 35.5 x 21.0 mm
