Nguyen-code/TVCRocket/Mechanical Design/manf/guidance mount top.STL

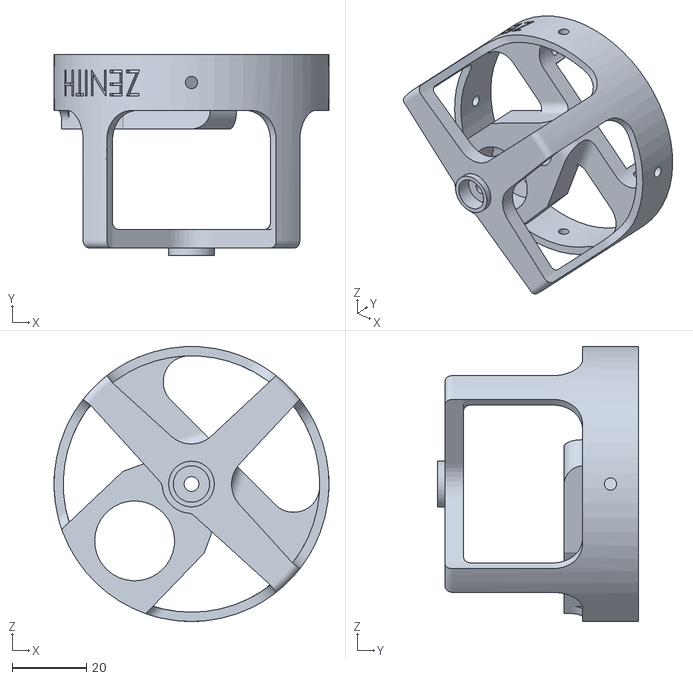
[picture p73: CAD file, 2020-10-10]
Mechanical Design/manf/guidance mount top.STL
74.0 x 54.0 x 74.0
