Nguyen-code/TVCRocket/Mechanical Design/coupler.SLDPRT

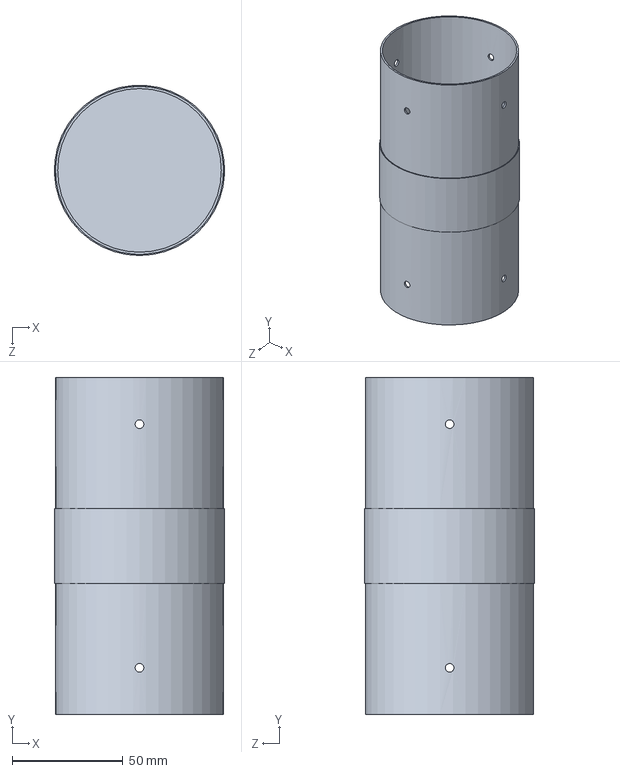
[picture p74: CAD file, 2020-10-02]
Mechanical Design/coupler.SLDPRT
76.9 x 152.4 x 76.9 mm
