Nguyen-code/TVCRocket/Mechanical Design/guidanceComputerMount/guidance computer.SLDPRT

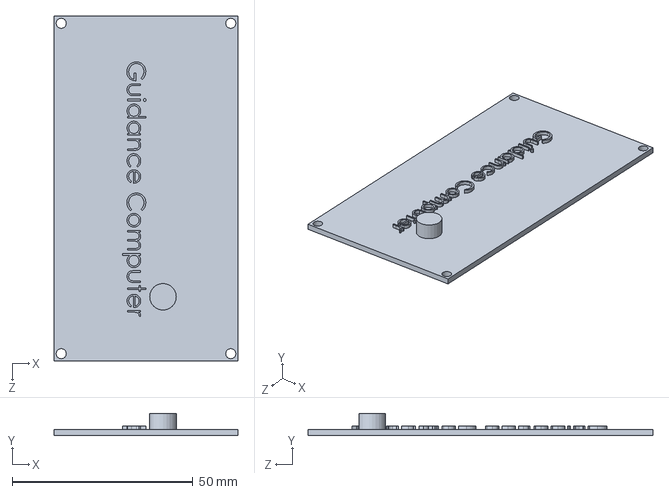
[picture p75: CAD file, 2020-10-02]
Mechanical Design/guidanceComputerMount/guidance computer.SLDPRT
50.9 x 6.15 x 95.4 mm
