Nguyen-code/TVCRocket/Mechanical Design/manf/gear1.STL

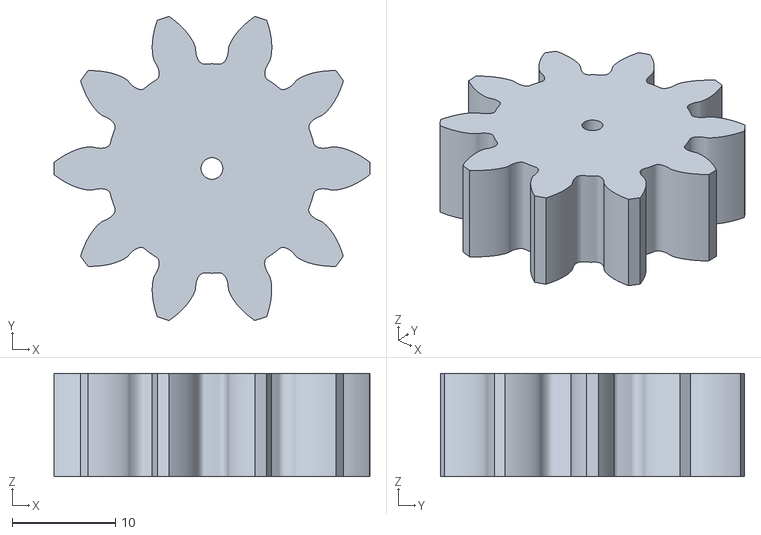
[picture p76: CAD file, 2020-10-10]
Mechanical Design/manf/gear1.STL
30.6 x 29.4 x 10.0
