Nguyen-code/TVCRocket/Mechanical Design/FIXME piston bulkhead.SLDPRT

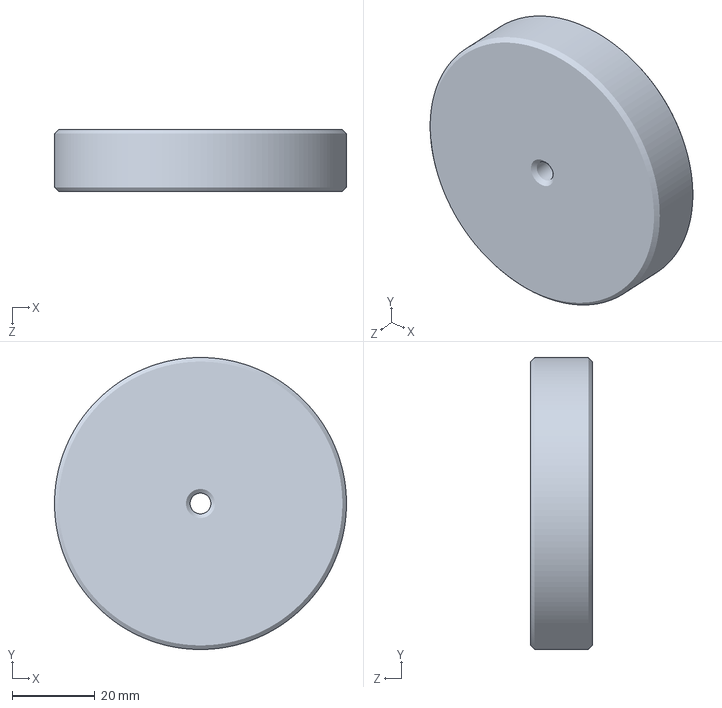
[picture p77: CAD file, 2020-09-28]
Mechanical Design/FIXME piston bulkhead.SLDPRT
70.5 x 70.5 x 15.0 mm
