Nguyen-code/TVCRocket/Mechanical Design/manf/topMountP2.sldprt

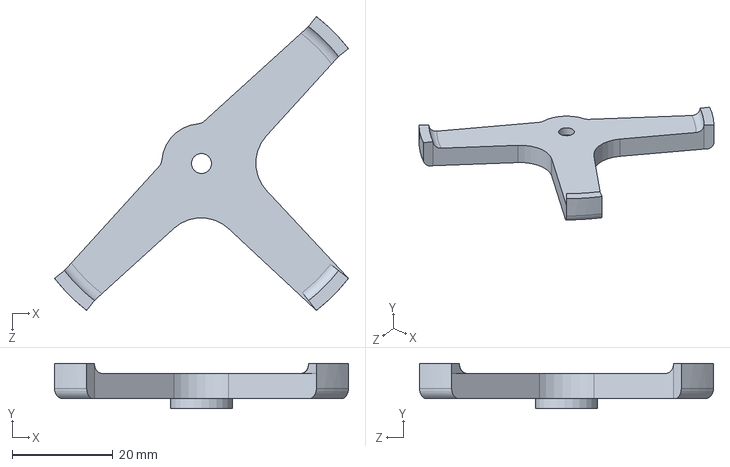
[picture p78: CAD file, 2020-10-10]
Mechanical Design/manf/topMountP2.sldprt
58.3 x 9.00 x 58.3 mm
