Nguyen-code/TVCRocket/Mechanical Design/manf/gimbalOuter.STL

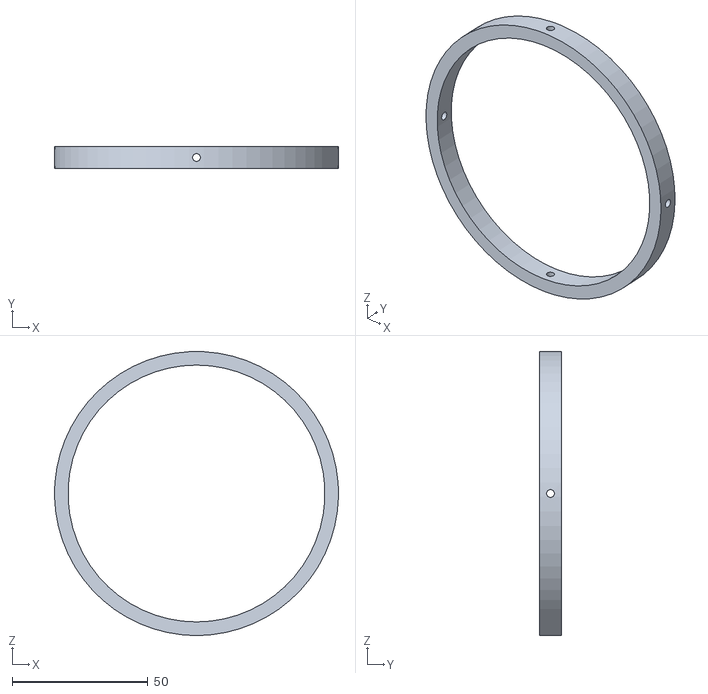
[picture p79: CAD file, 2020-10-10]
Mechanical Design/manf/gimbalOuter.STL
104.5 x 8.00 x 104.5
