Nguyen-code/TVCRocket/Mechanical Design/manf/gear2.STL

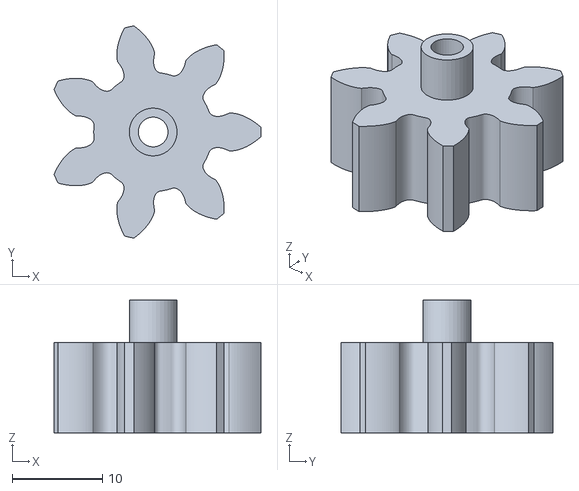
[picture p80: CAD file, 2020-10-10]
Mechanical Design/manf/gear2.STL
23.0 x 23.6 x 14.7
