Nguyen-code/TVCRocket/Mechanical Design/manf/topMountP2v2.sldprt

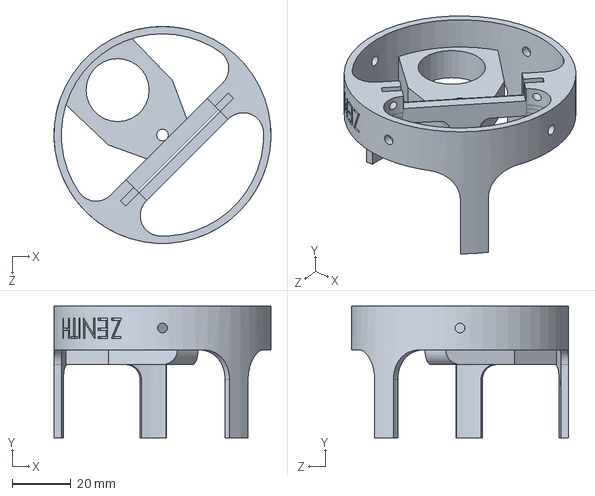
[picture p81: CAD file, 2020-10-10]
Mechanical Design/manf/topMountP2v2.sldprt
74.0 x 45.0 x 74.0 mm
