Nguyen-code/TVCRocket/Mechanical Design/manf/nosecone.STL

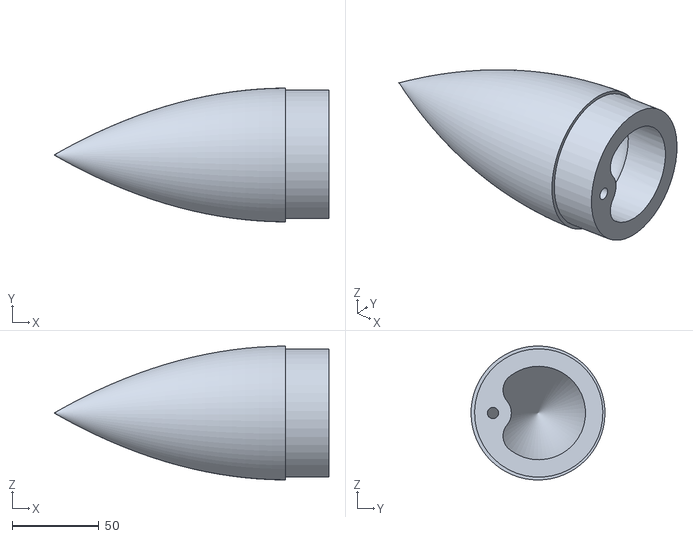
[picture p82: CAD file, 2020-09-28]
Mechanical Design/manf/nosecone.STL
158.1 x 77.0 x 77.0
