Nguyen-code/TVCRocket/Mechanical Design/manf/BPS_Piston_Ejection_-_Coupler_Bulkhead.stl

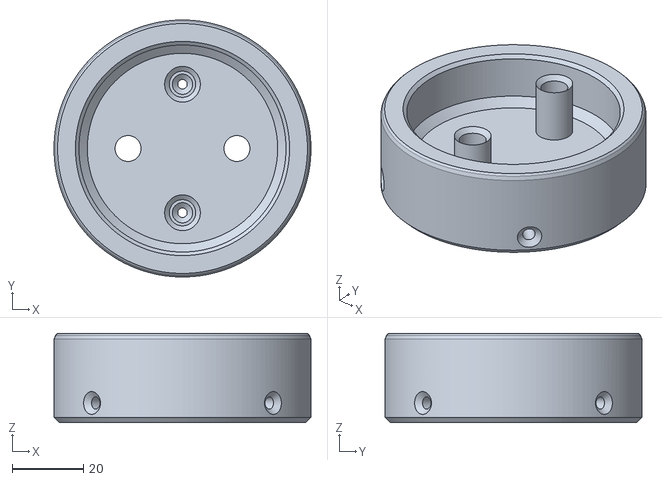
[picture p83: CAD file, 2020-09-26]
Mechanical Design/manf/BPS_Piston_Ejection_-_Coupler_Bulkhead.stl
72.0 x 72.0 x 25.0
