Nguyen-code/TVCRocket/Software/Reference/arm debuggers.jpg

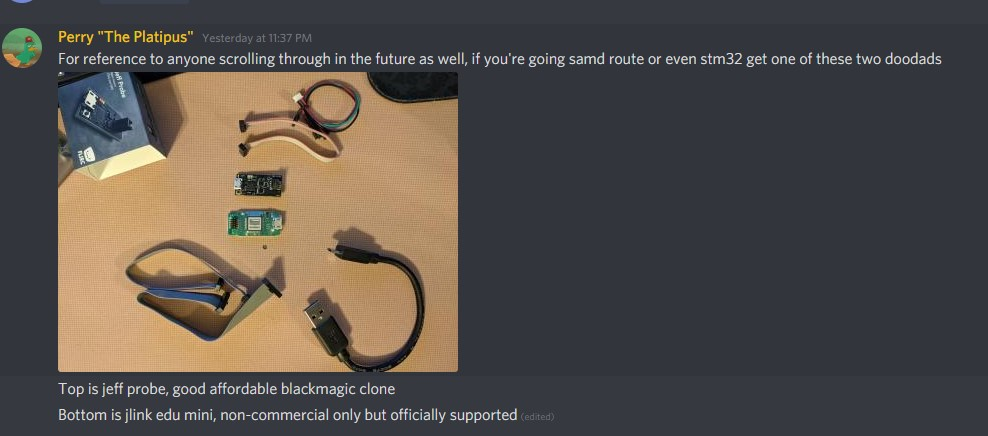
Software/Reference/arm debuggers.jpg
